Hallaz/KLORID/hardware/case/Alternate Case Design/Tenting Legs/images/choc-sofle-2.jpg

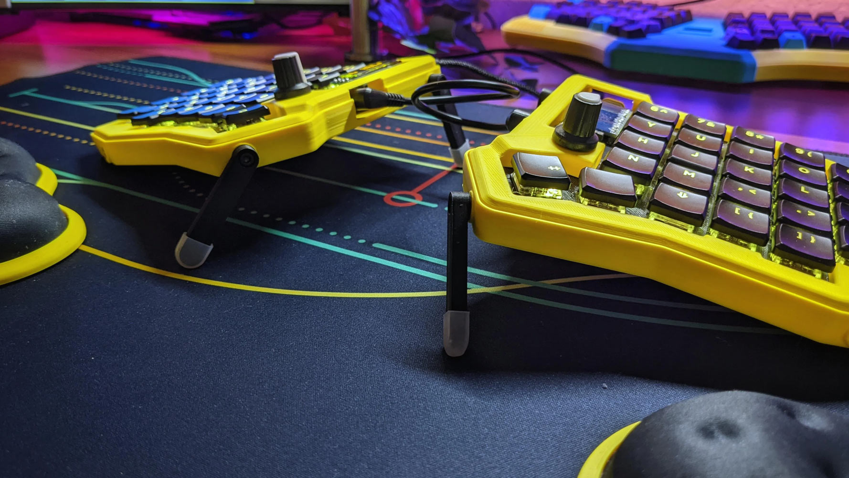
hardware/case/Alternate Case Design/Tenting Legs/images/choc-sofle-2.jpg
