Hallaz/KLORID/hardware/case/Alternate Case Design/Tenting Legs/images/tentingLeg26mm.png

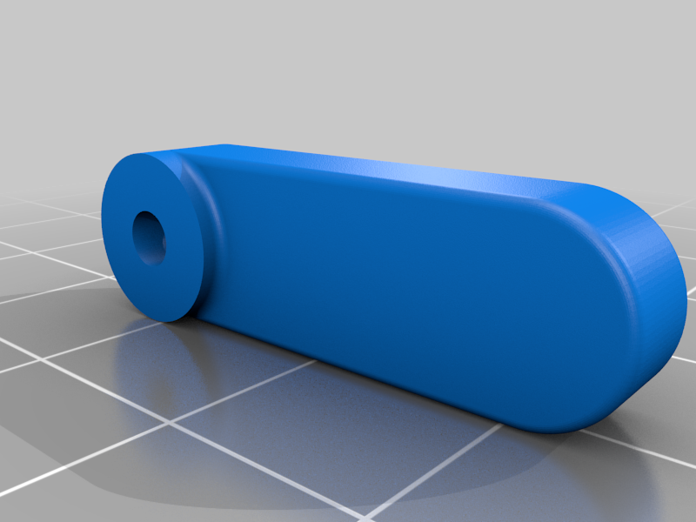
hardware/case/Alternate Case Design/Tenting Legs/images/tentingLeg26mm.png
