Hallaz/KLORID/hardware/case/Alternate Case Design/Tenting Legs/images/TentingLeg38mm.png

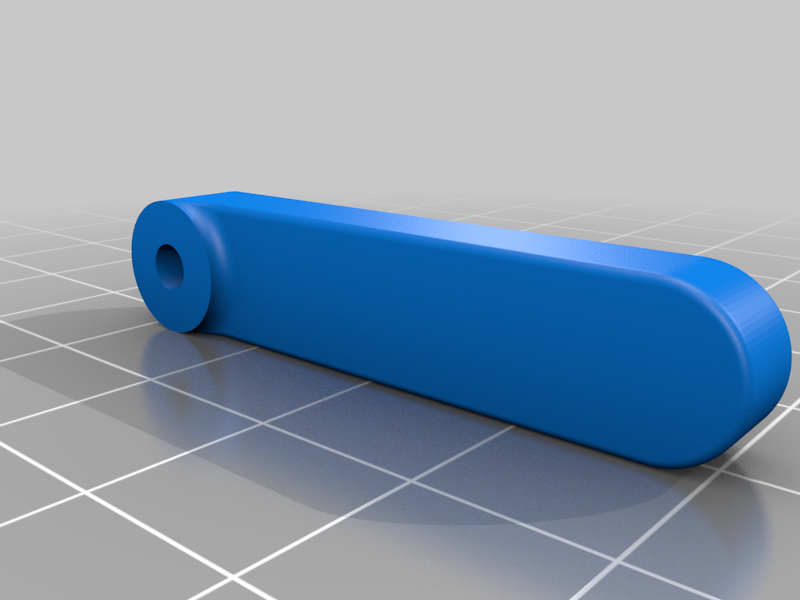
hardware/case/Alternate Case Design/Tenting Legs/images/TentingLeg38mm.png
