Hallaz/KLORID/hardware/case/Alternate Case Design/Tenting Legs/images/tentingLegALT31mm.png

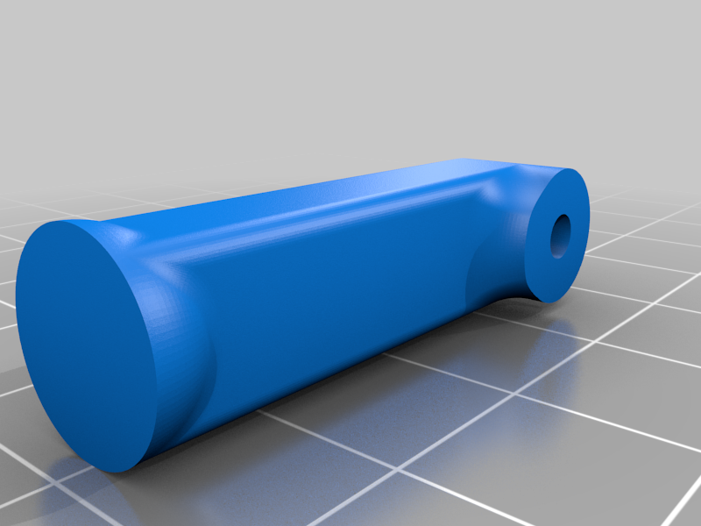
hardware/case/Alternate Case Design/Tenting Legs/images/tentingLegALT31mm.png
