Hallaz/KLORID/hardware/case/Alternate Case Design/Tenting Legs/images/tentingLegALT37mm.png

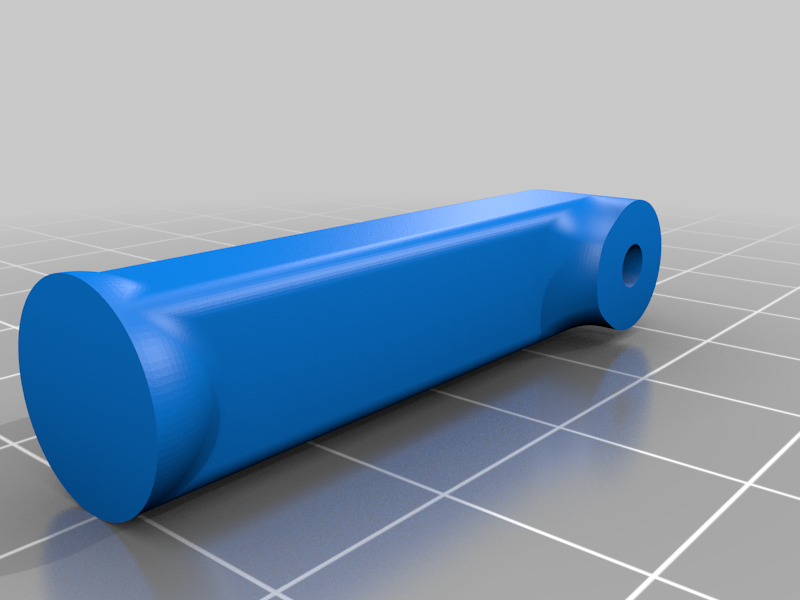
hardware/case/Alternate Case Design/Tenting Legs/images/tentingLegALT37mm.png
