Hallaz/KLORID/hardware/case/docs/images/konrad_3dp.png

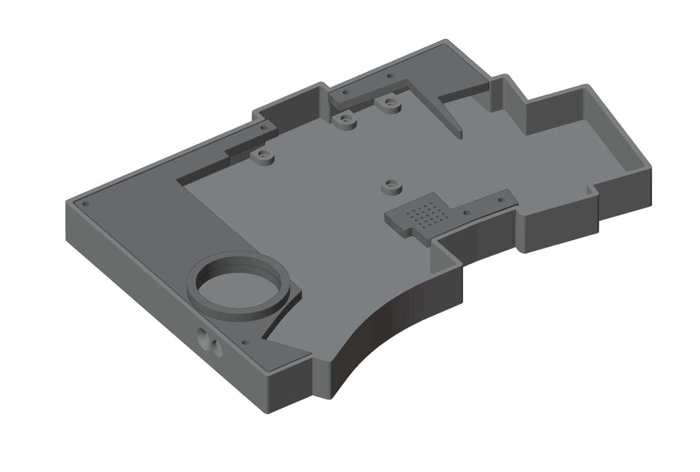
hardware/case/docs/images/konrad_3dp.png
