Hallaz/KLORID/hardware/case/docs/images/konrad_acryl.png

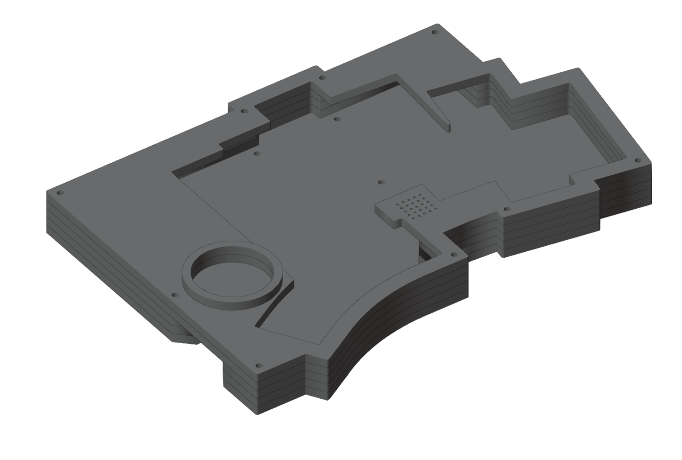
hardware/case/docs/images/konrad_acryl.png
