Hallaz/KLORID/hardware/case/docs/images/saegewerk_3dp_ble_puck.png

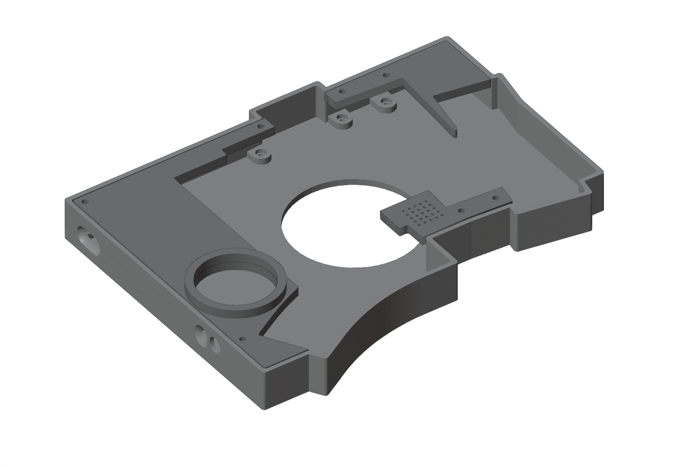
hardware/case/docs/images/saegewerk_3dp_ble_puck.png
