Hallaz/KLORID/hardware/case/docs/images/yubitsume_3dp.png

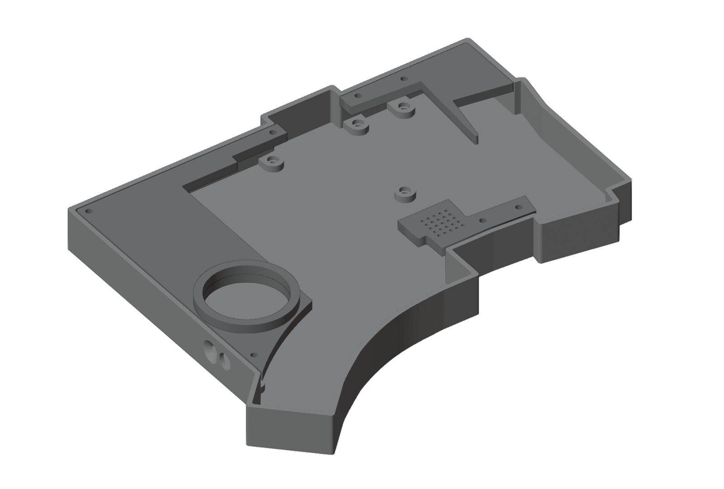
hardware/case/docs/images/yubitsume_3dp.png
