Hallaz/KLORID/hardware/docs/images/Klor_1.4_picture1.png

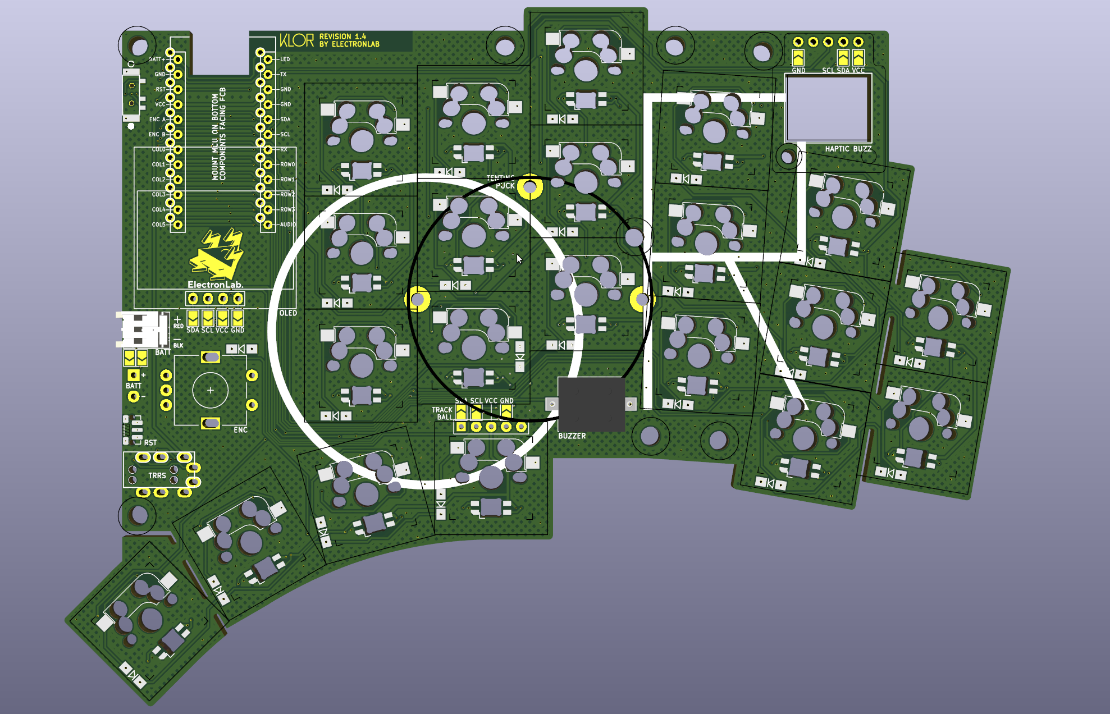
hardware/docs/images/Klor_1.4_picture1.png
