Hallaz/KLORID/hardware/docs/images/Klor_1.4_picture2.png

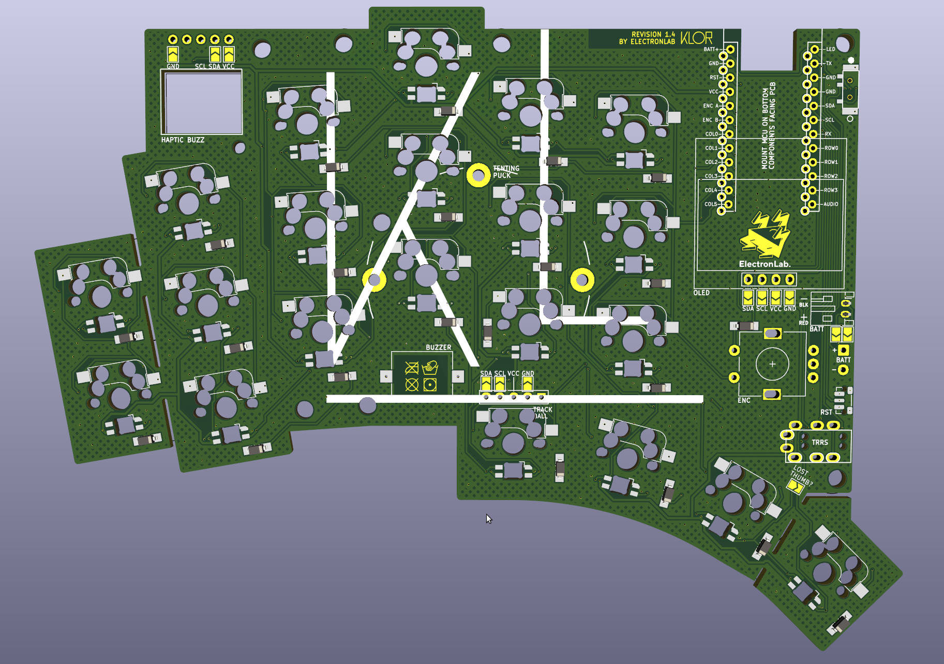
hardware/docs/images/Klor_1.4_picture2.png
