Hallaz/KLORID/hardware/docs/images/Klor_1.4_picture3.png

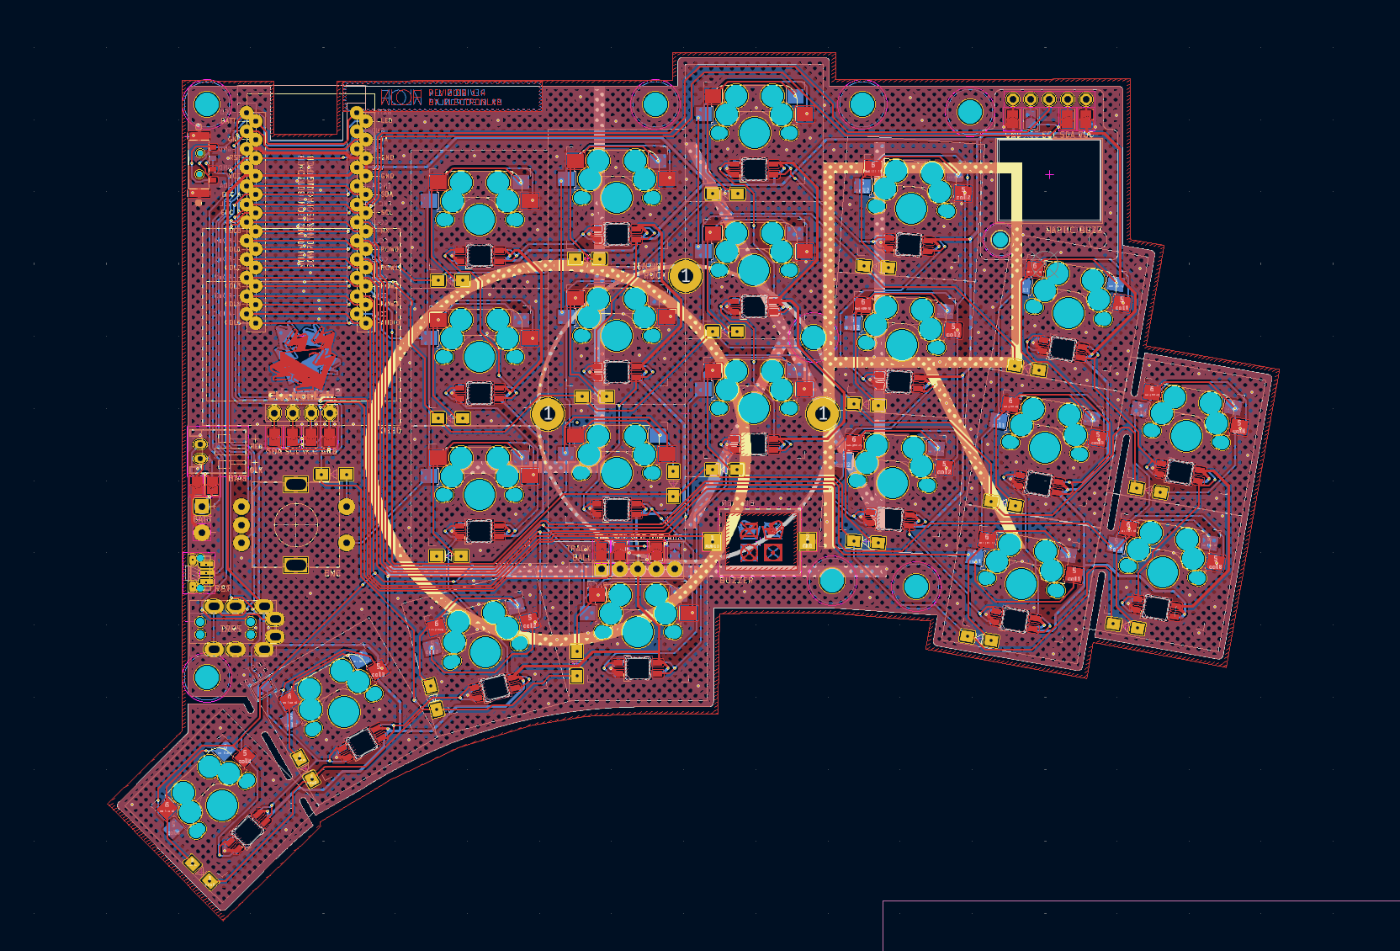
hardware/docs/images/Klor_1.4_picture3.png
