Hallaz/KLORID/hardware/docs/images/Klor_1.4_picture4.png

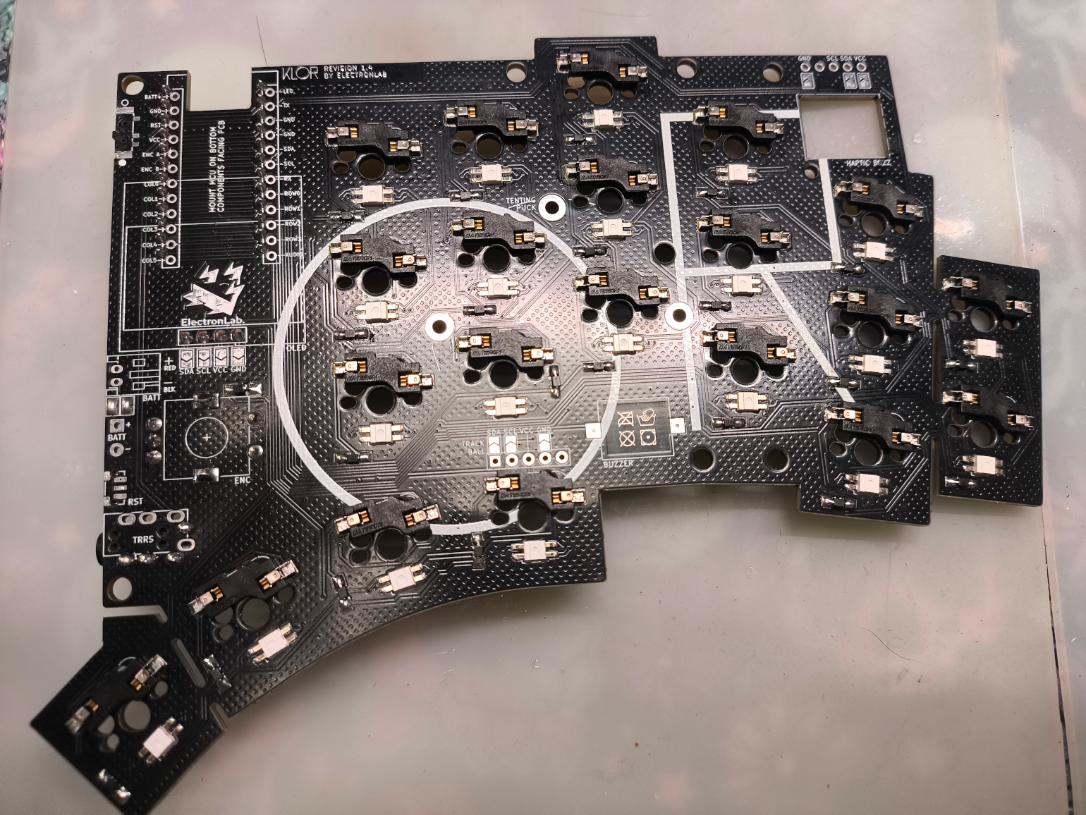
hardware/docs/images/Klor_1.4_picture4.png
