Hallaz/KLORID/hardware/docs/images/Klor_1.4_picture5.png

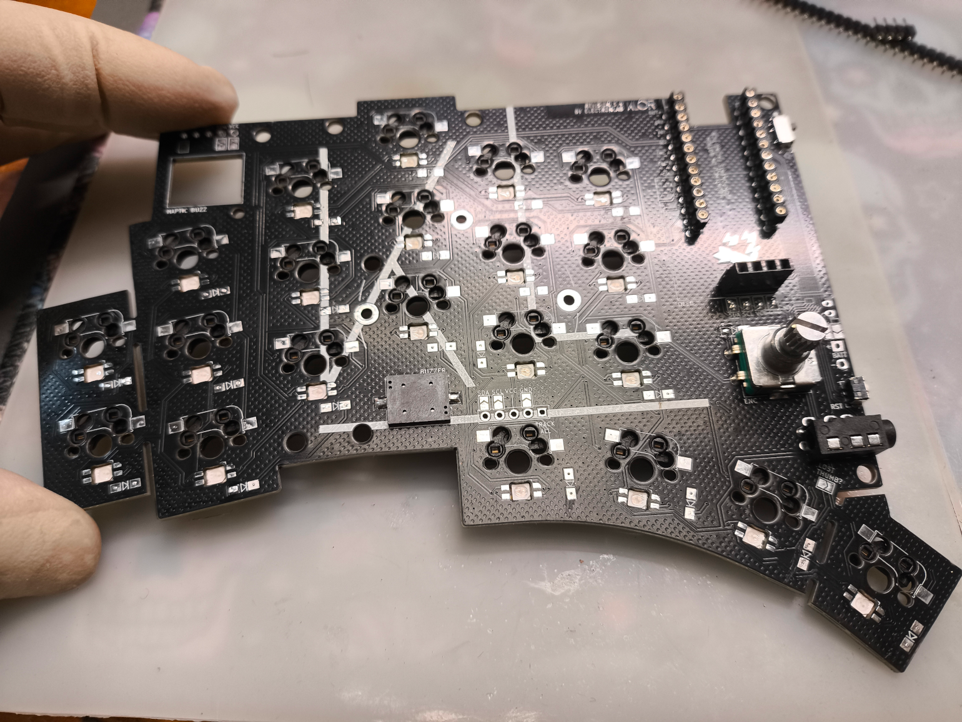
hardware/docs/images/Klor_1.4_picture5.png
