Hallaz/KLORID/hardware/docs/images/Klor_1.4_picture7.png

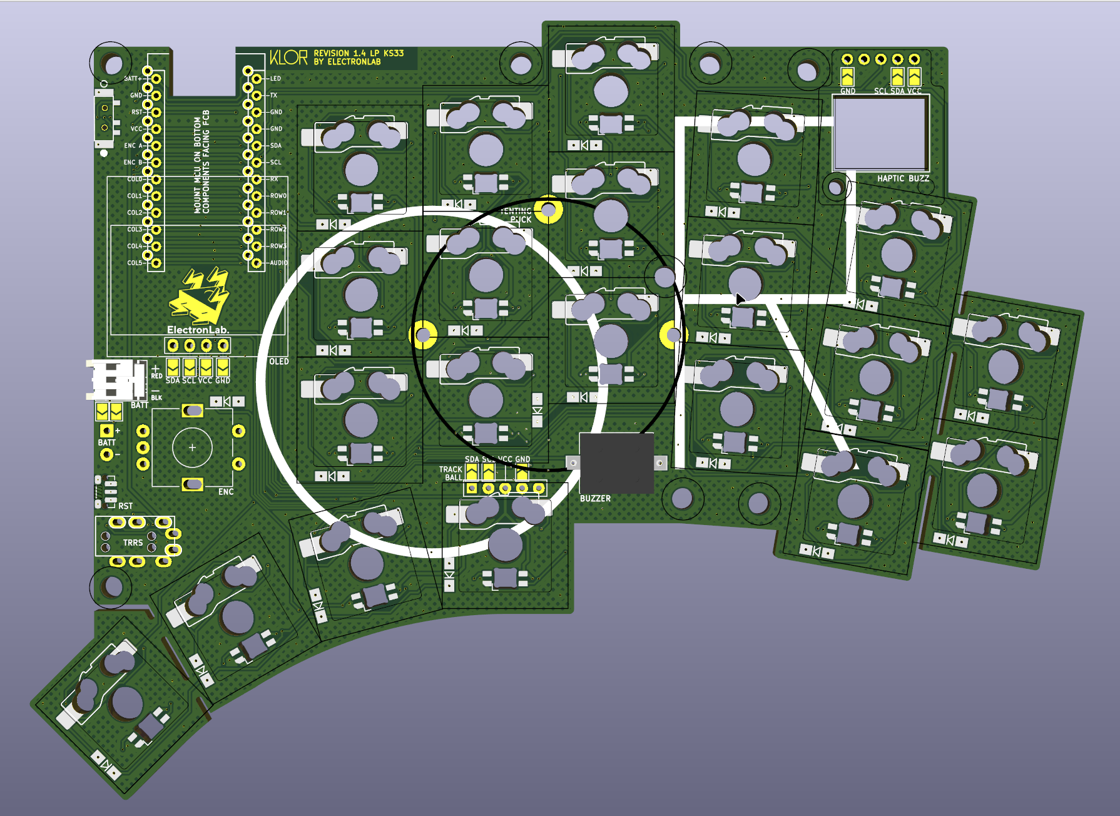
hardware/docs/images/Klor_1.4_picture7.png
