Hallaz/KLORID/hardware/docs/images/Klor_1.4_picture10.png

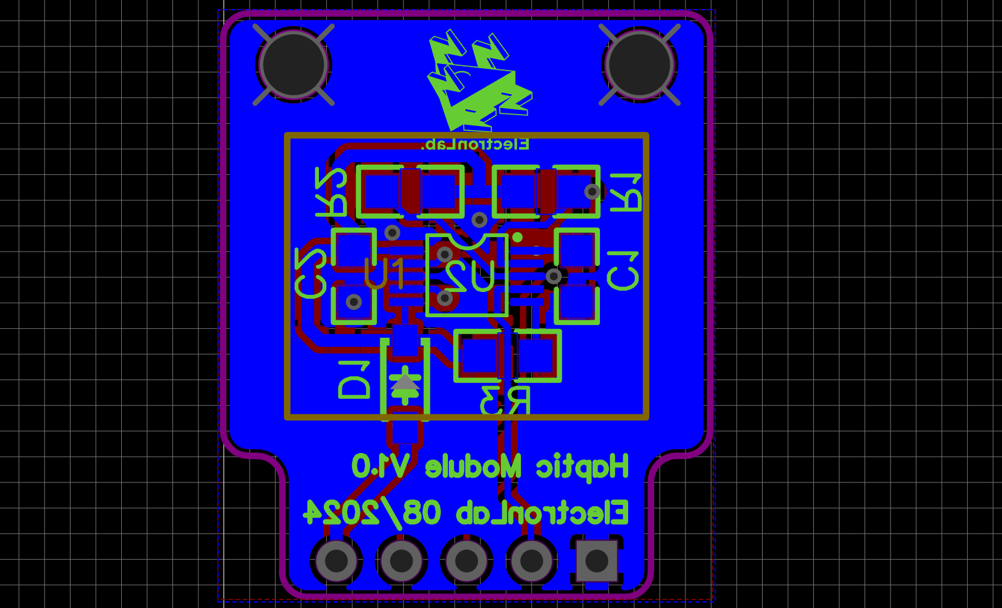
hardware/docs/images/Klor_1.4_picture10.png
