Hallaz/KLORID/hardware/docs/images/Klor_1.4_picture11.png

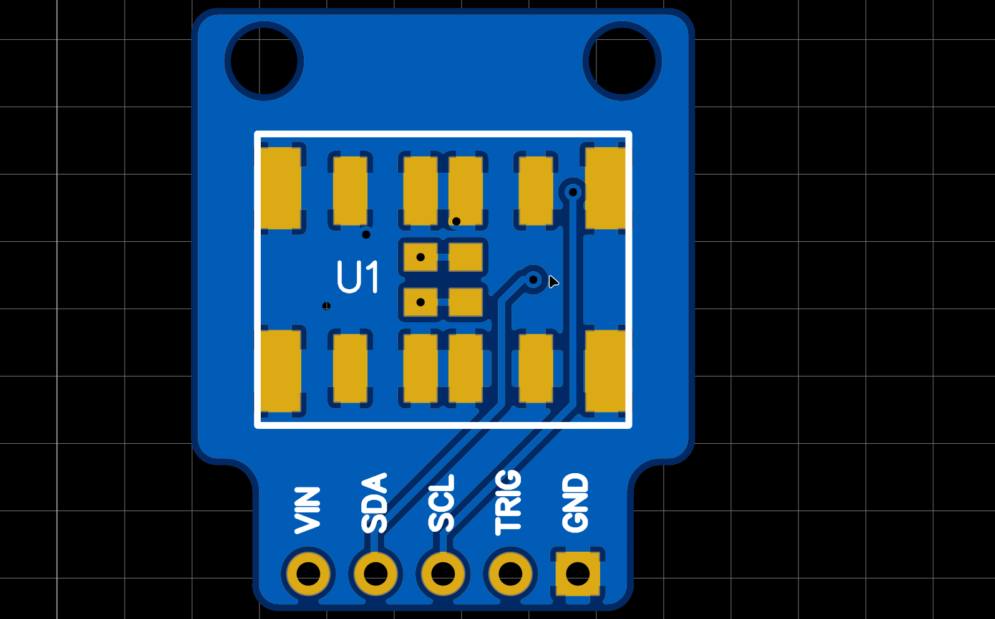
hardware/docs/images/Klor_1.4_picture11.png
