Hallaz/KLORID/hardware/docs/images/Klor_1.4_picture12.png

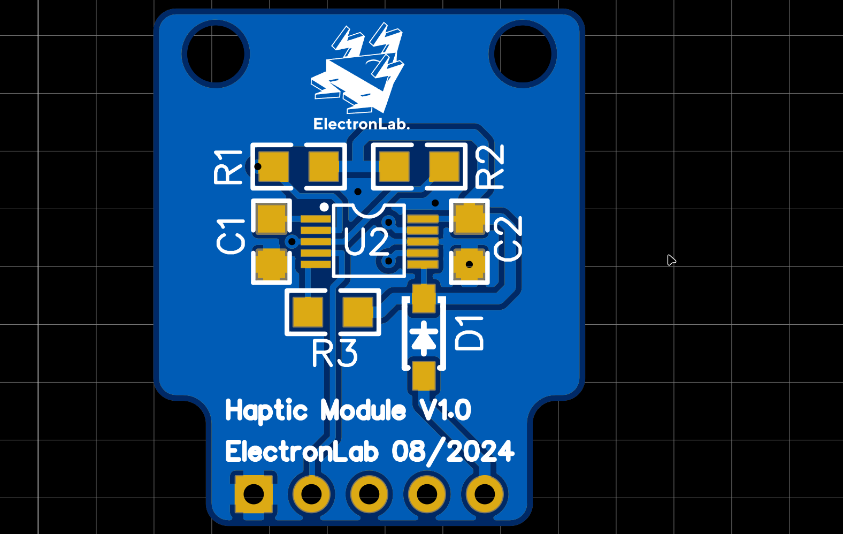
hardware/docs/images/Klor_1.4_picture12.png
