Hallaz/KLORID/hardware/docs/images/Klor_1.4_picture13.png

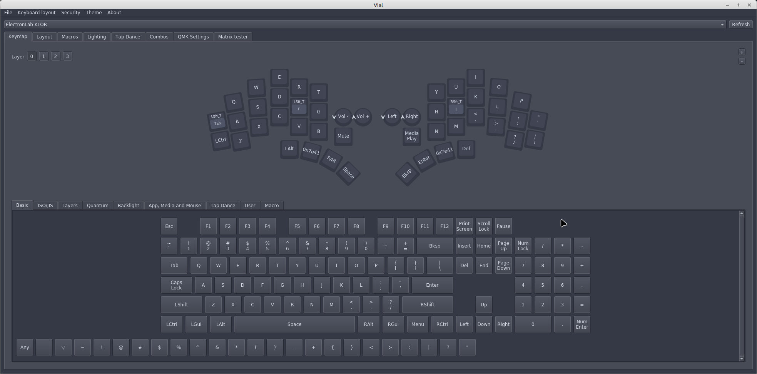
hardware/docs/images/Klor_1.4_picture13.png
