Hallaz/KLORID/hardware/docs/images/KLOR_1.5_picture1.png

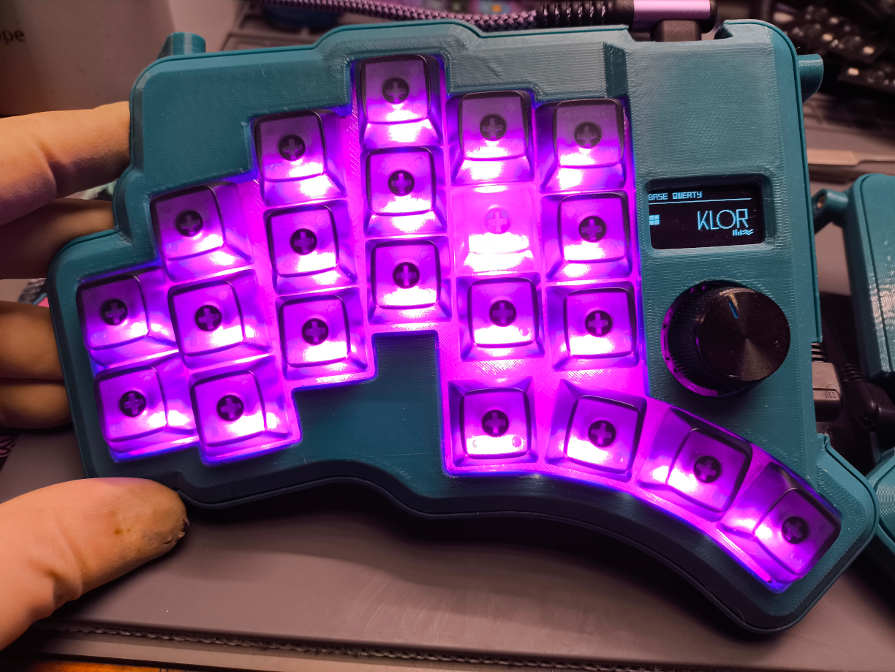
hardware/docs/images/KLOR_1.5_picture1.png
