Hallaz/KLORID/hardware/docs/images/KLOR_1.5_picture2.png

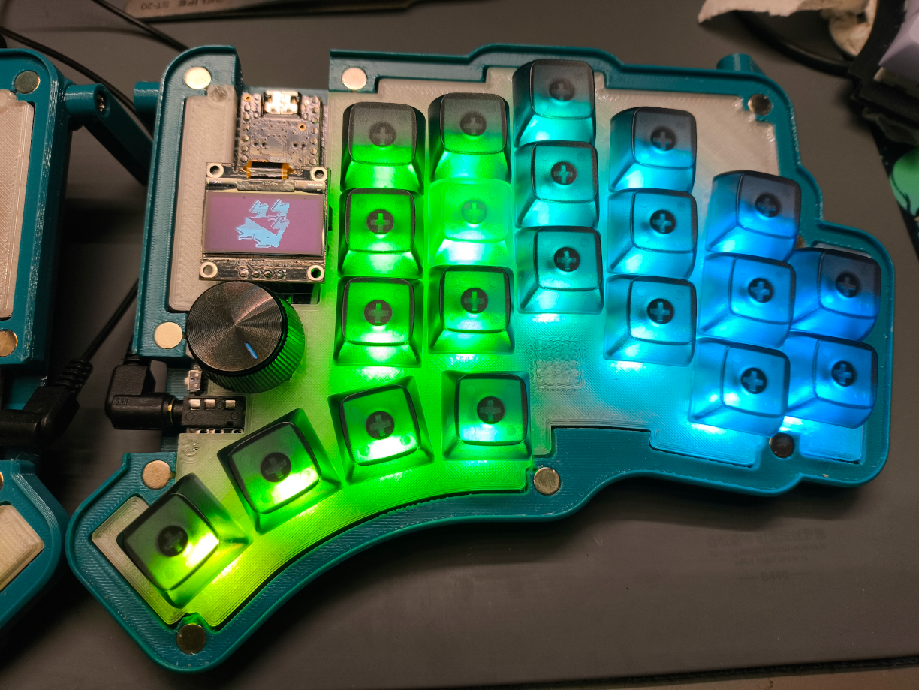
hardware/docs/images/KLOR_1.5_picture2.png
