Hallaz/KLORID/hardware/docs/images/KLOR_1.5_picture4.png

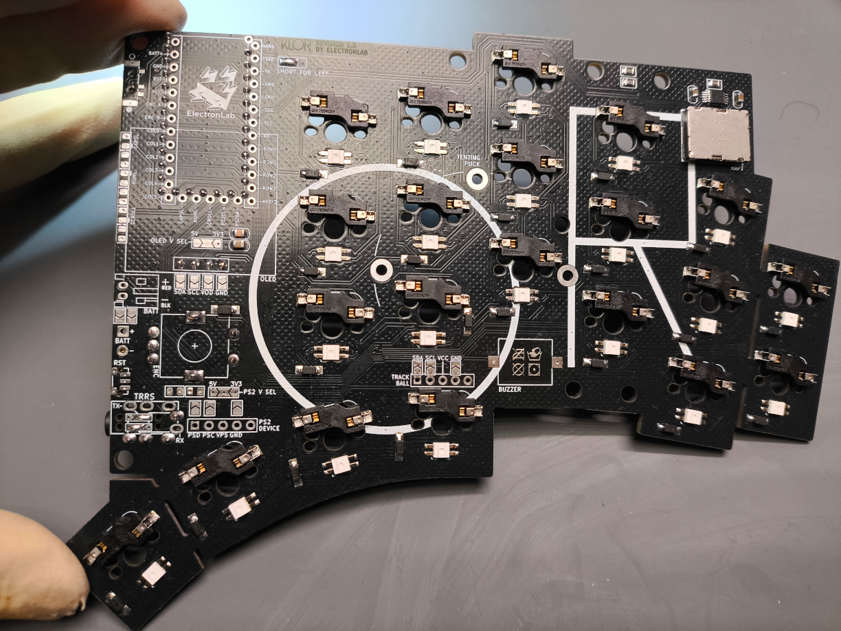
hardware/docs/images/KLOR_1.5_picture4.png
