Hallaz/KLORID/hardware/docs/images/KLOR_1.5_picture5.png

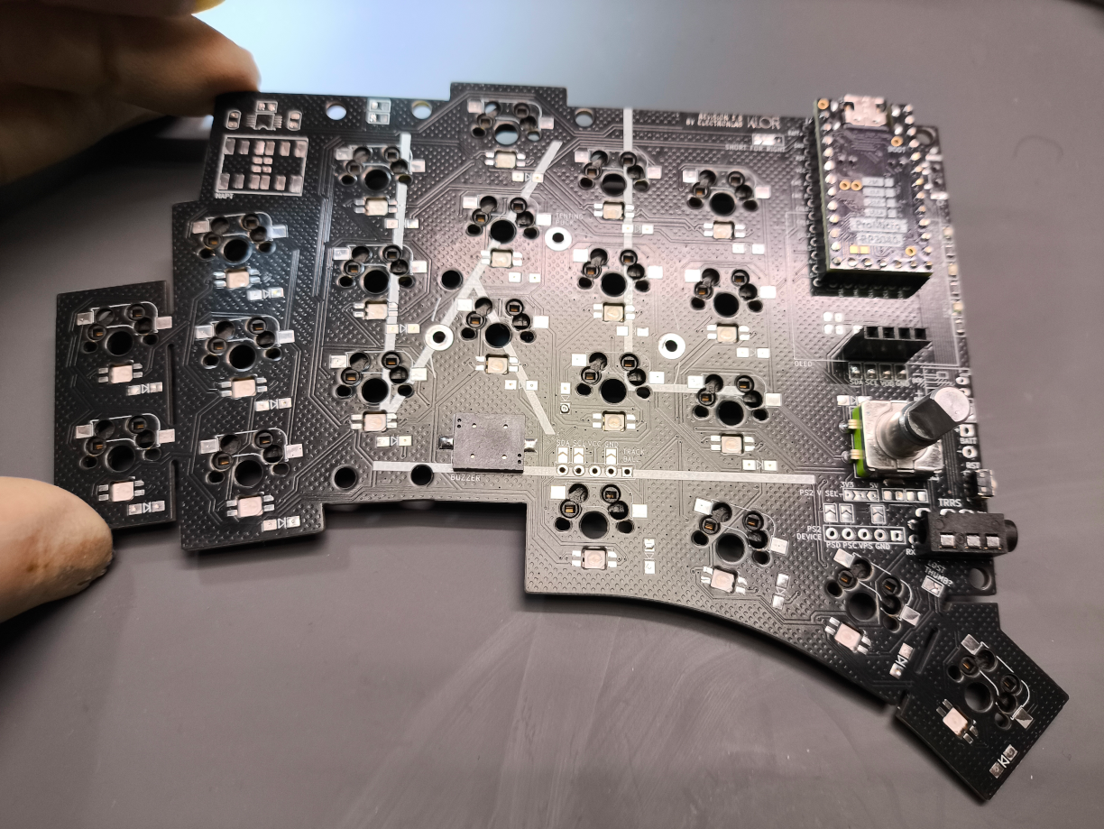
hardware/docs/images/KLOR_1.5_picture5.png
