Hallaz/KLORID/hardware/docs/images/KLOR_knob1-2.png

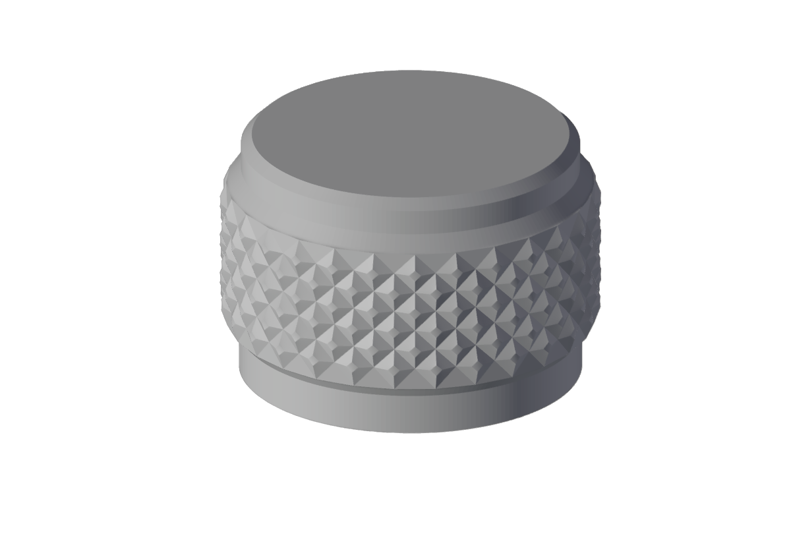
hardware/docs/images/KLOR_knob1-2.png
