Hallaz/KLORID/hardware/docs/images/KLOR_knob_resin_nylon.jpg

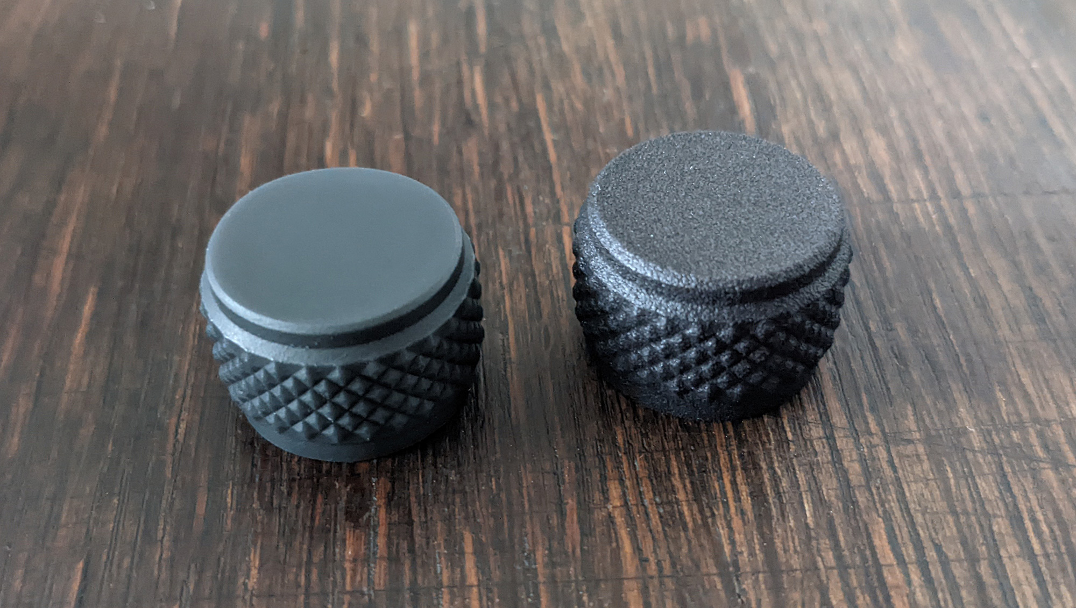
hardware/docs/images/KLOR_knob_resin_nylon.jpg
