Hallaz/KLORID/hardware/docs/images/KLOR_polydactyl_DES01.jpg

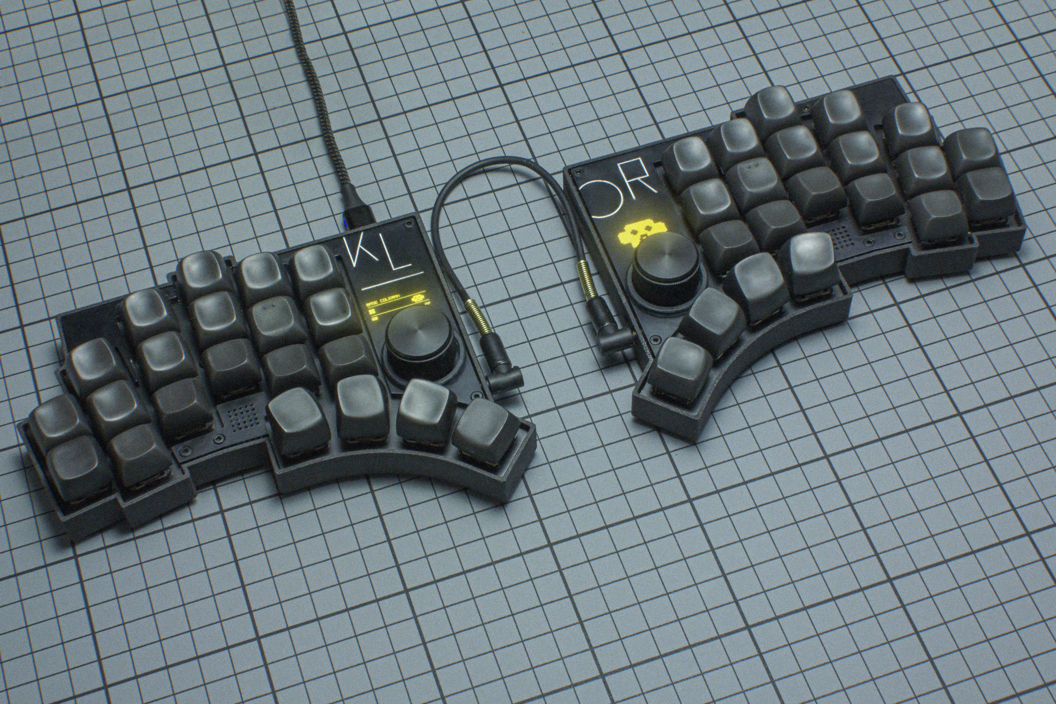
hardware/docs/images/KLOR_polydactyl_DES01.jpg
