Hallaz/KLORID/hardware/docs/images/KLOR_polydactyl_DES02.jpg

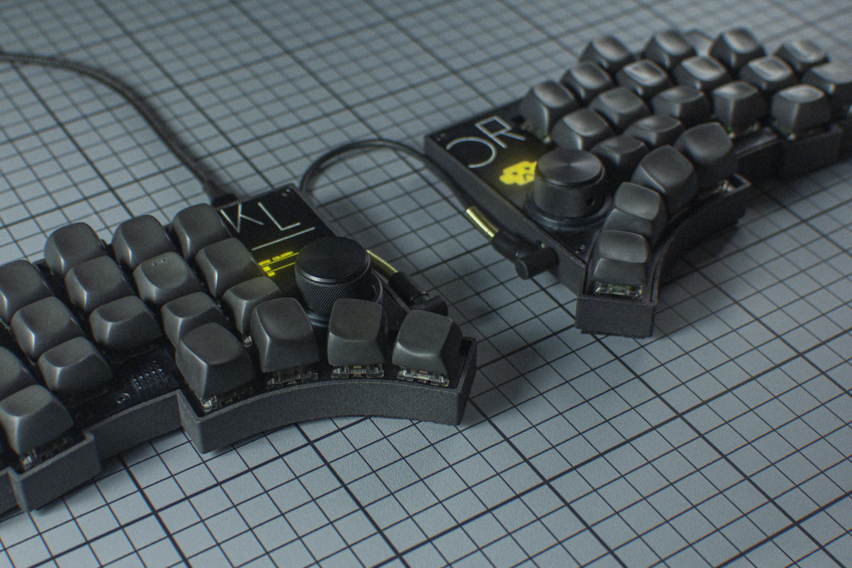
hardware/docs/images/KLOR_polydactyl_DES02.jpg
