Hallaz/KLORID/hardware/docs/images/KLOR_saegewerk_GRID01.jpg

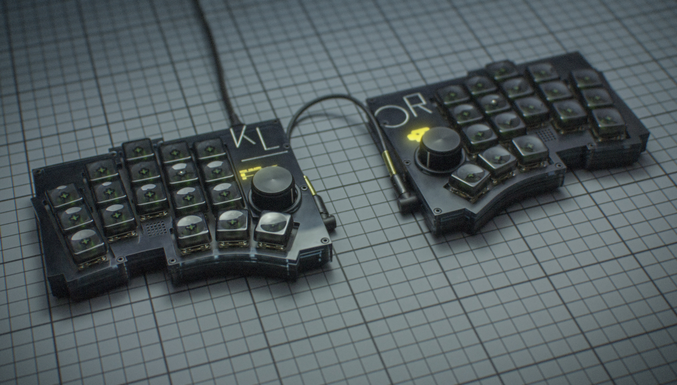
hardware/docs/images/KLOR_saegewerk_GRID01.jpg
