Hallaz/KLORID/hardware/docs/images/KLOR_saegewerk_GRID02.jpg

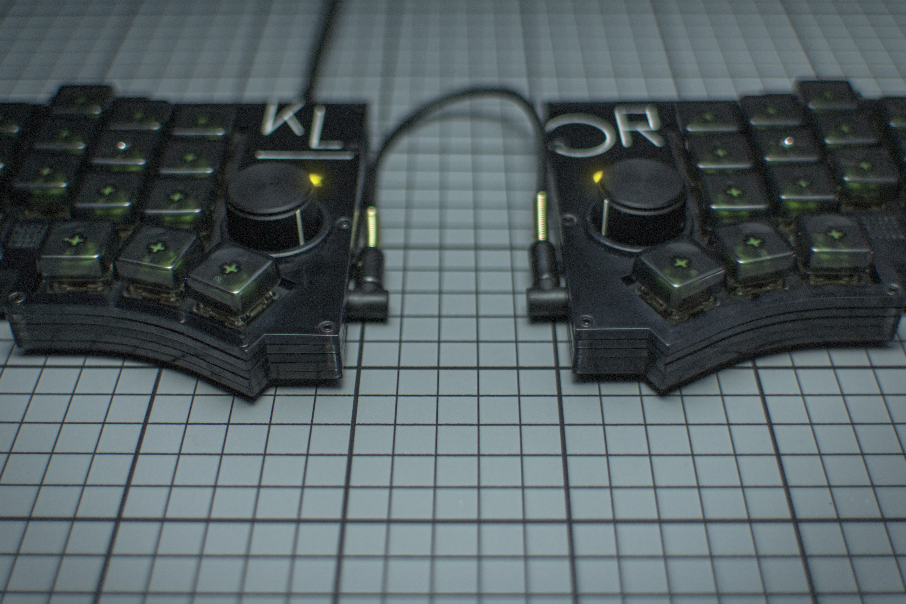
hardware/docs/images/KLOR_saegewerk_GRID02.jpg
