Hallaz/KLORID/hardware/docs/images/KLORpcb.png

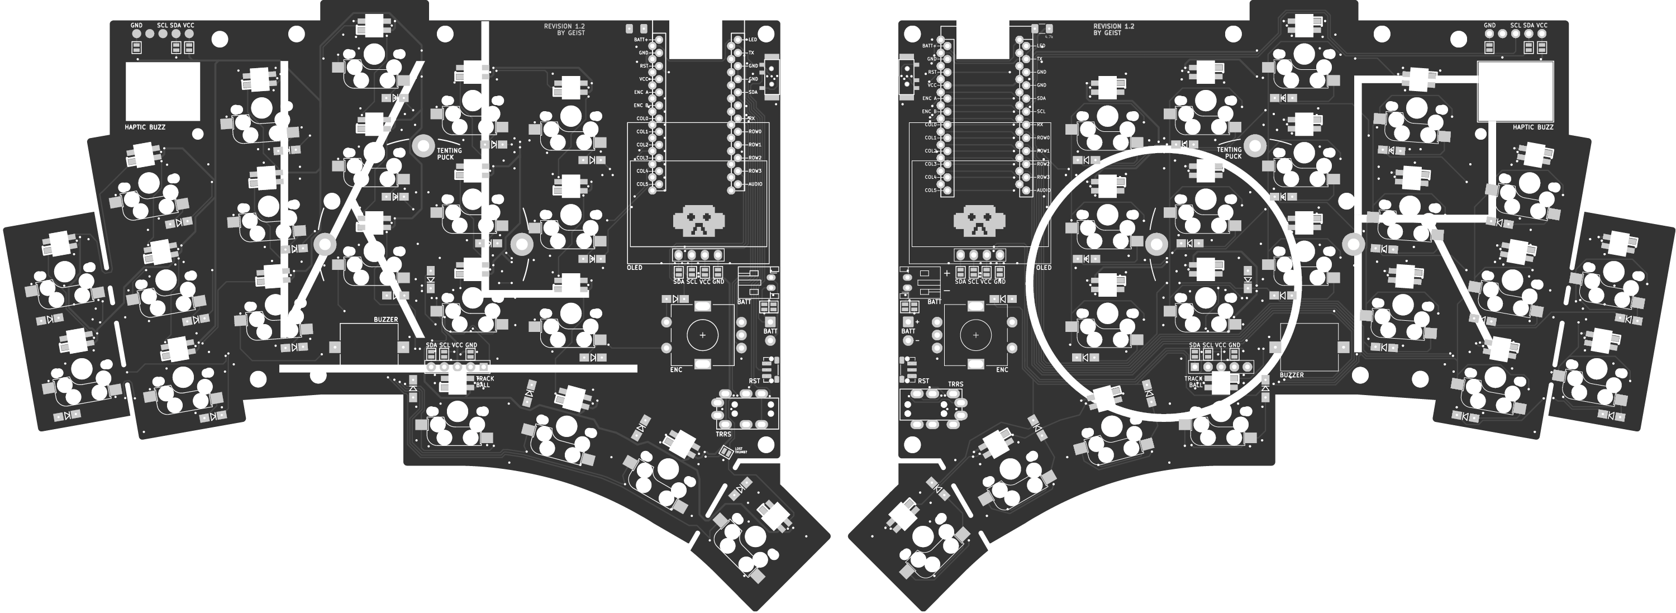
hardware/docs/images/KLORpcb.png
