Hallaz/KLORID/hardware/docs/images/KLORpinout.png

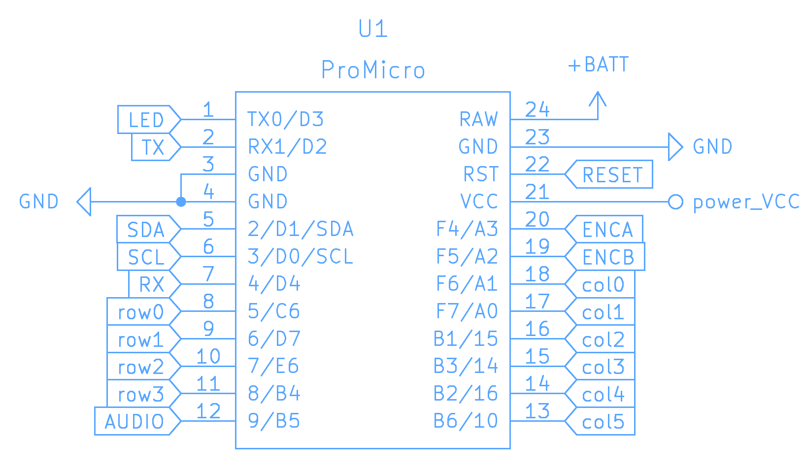
hardware/docs/images/KLORpinout.png
