Hallaz/KLORID/hardware/docs/images/KLORtraces.png

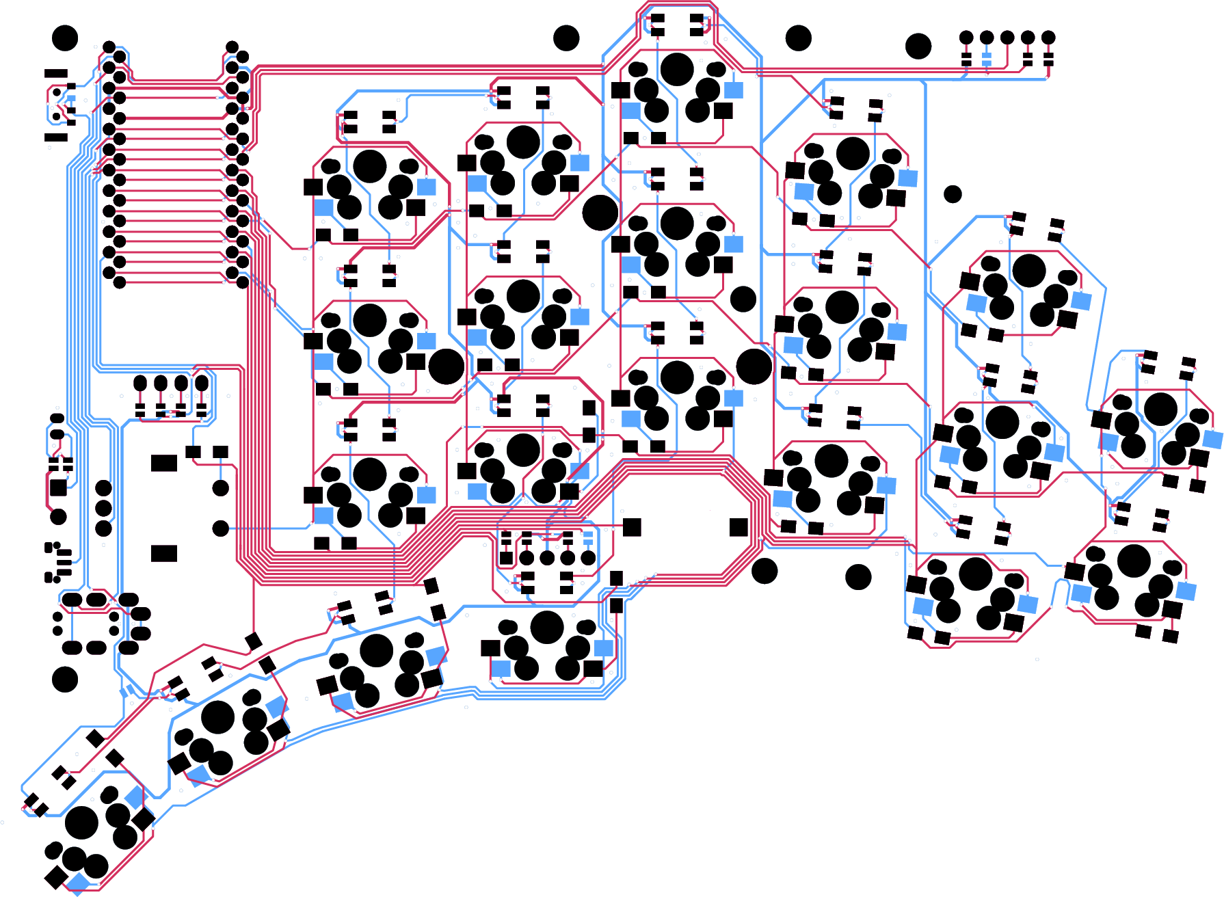
hardware/docs/images/KLORtraces.png
