Hallaz/KLORID/hardware/case/Alternate Case Design/Konrad/BaseWithTenting-Konrad.stl

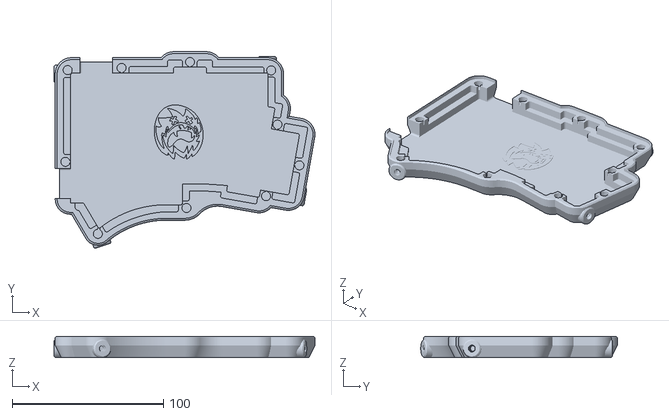
[picture p56: CAD file, 2026-05-15]
hardware/case/Alternate Case Design/Konrad/BaseWithTenting-Konrad.stl
172.8 x 130.1 x 14.0
