Hallaz/KLORID/hardware/case/Alternate Case Design/Polydactyl/v2-GasketBase.stl

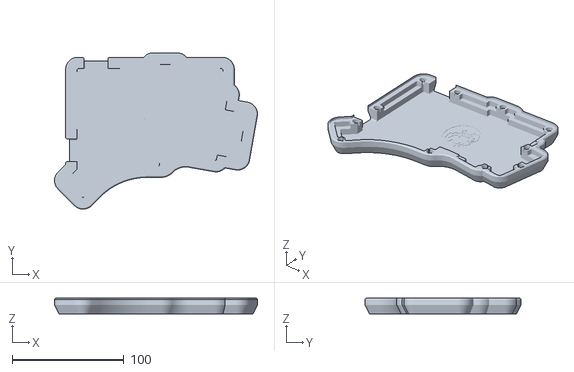
[picture p57: CAD file, 2026-05-15]
hardware/case/Alternate Case Design/Polydactyl/v2-GasketBase.stl
182.0 x 140.1 x 14.0
