Hallaz/KLORID/hardware/case/Alternate Case Design/Saegewerk/v1-Base-Saegewerk.stl

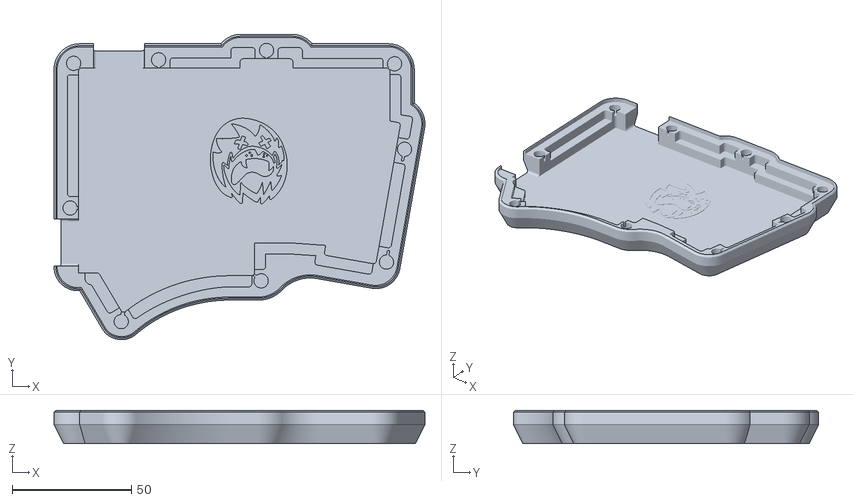
[picture p58: CAD file, 2026-05-15]
hardware/case/Alternate Case Design/Saegewerk/v1-Base-Saegewerk.stl
155.7 x 128.2 x 14.0
