Hallaz/KLORID/hardware/case/Alternate Case Design/Tenting Legs/files/tentingLeg42mm.stl

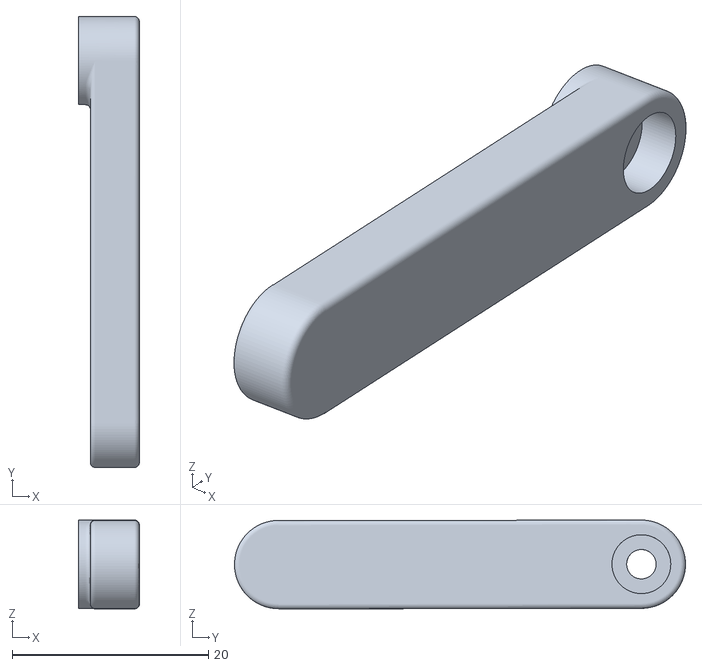
[picture p59: CAD file, 2026-05-15]
hardware/case/Alternate Case Design/Tenting Legs/files/tentingLeg42mm.stl
6.21 x 46.0 x 9.07
