Hallaz/KLORID/hardware/case/Alternate Case Design/Yubitsume/v1-Base-Yubitmsume.stl

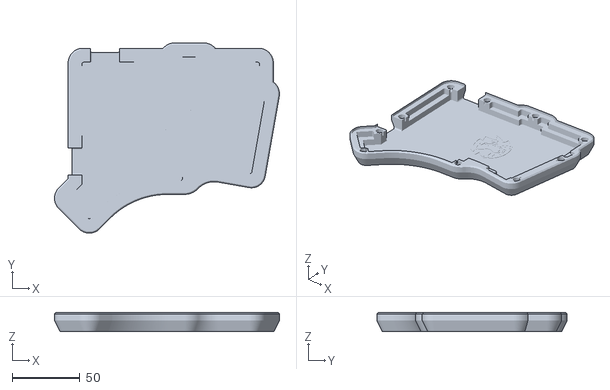
[picture p60: CAD file, 2026-05-15]
hardware/case/Alternate Case Design/Yubitsume/v1-Base-Yubitmsume.stl
165.8 x 140.1 x 14.0
