Hallaz/KLORID/hardware/case/3DP/konrad/acrylic/KLOR_konrad_3DPcase_acrylic_logotype.dxf

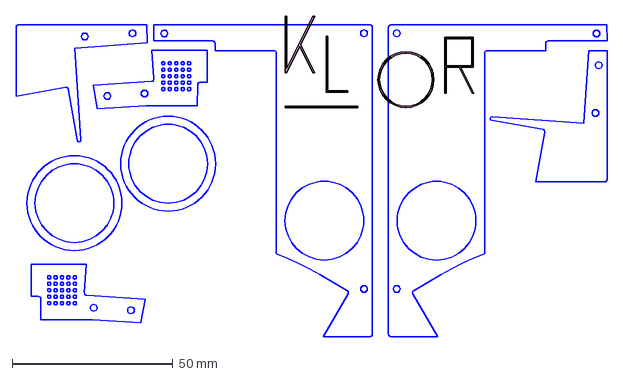
[picture p61: CAD file, 2026-05-15]
hardware/case/3DP/konrad/acrylic/KLOR_konrad_3DPcase_acrylic_logotype.dxf
183.6 x 99.5 mm
