Hallaz/KLORID/hardware/case/3DP/konrad/regular/KLOR_konrad_case_L.stl

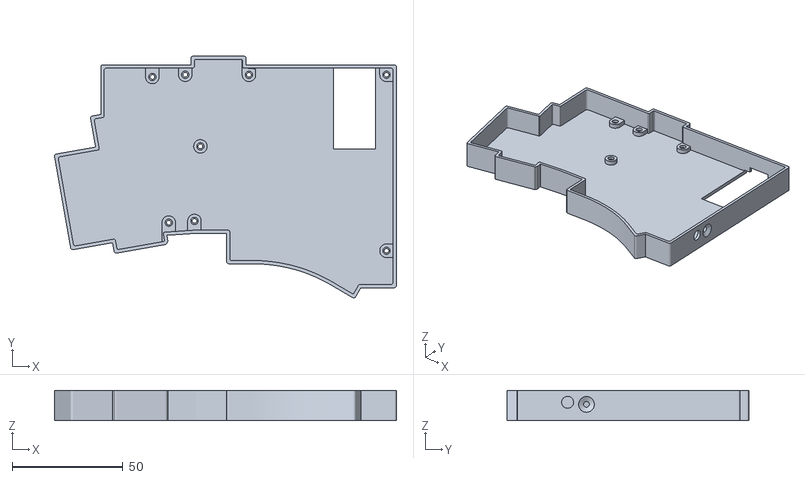
[picture p62: CAD file, 2026-05-15]
hardware/case/3DP/konrad/regular/KLOR_konrad_case_L.stl
154.3 x 109.2 x 13.6
