Hallaz/KLORID/hardware/case/3DP/polydactyl/acrylic/KLOR_polydactyl_3DPcase_acrylic_logotype.dxf

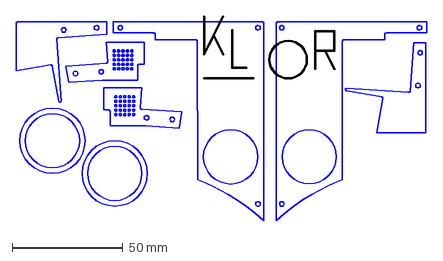
[picture p63: CAD file, 2026-05-15]
hardware/case/3DP/polydactyl/acrylic/KLOR_polydactyl_3DPcase_acrylic_logotype.dxf
185.0 x 92.4 mm
