Hallaz/KLORID/hardware/case/3DP/saegewerk/acrylic/KLOR_saegewerk_3DPcase_acrylic_logotype.dxf

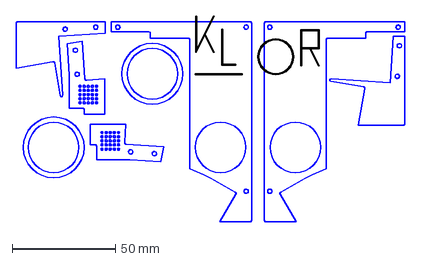
[picture p64: CAD file, 2026-05-15]
hardware/case/3DP/saegewerk/acrylic/KLOR_saegewerk_3DPcase_acrylic_logotype.dxf
188.1 x 99.5 mm
