Hallaz/KLORID/hardware/case/3DP/saegewerk/bluetooth/KLOR_saegewerk_case_ble_L.stl

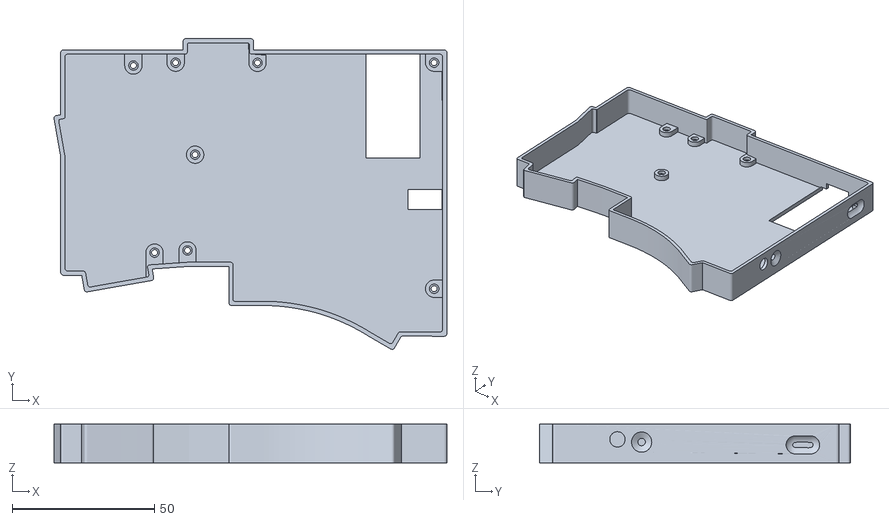
[picture p65: CAD file, 2026-05-15]
hardware/case/3DP/saegewerk/bluetooth/KLOR_saegewerk_case_ble_L.stl
138.1 x 109.2 x 13.6
