Hallaz/KLORID/hardware/case/3DP/yubitsume/acrylic/KLOR_yubitsume_3DPcase_acrylic_logotype.dxf

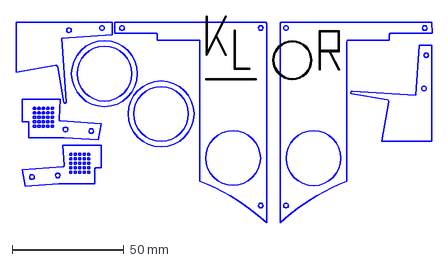
[picture p66: CAD file, 2026-05-15]
hardware/case/3DP/yubitsume/acrylic/KLOR_yubitsume_3DPcase_acrylic_logotype.dxf
186.0 x 92.4 mm
