Hallaz/KLORID/hardware/case/3DP/yubitsume/bluetooth/KLOR_yubitsume_case_puck_ble_R.stl

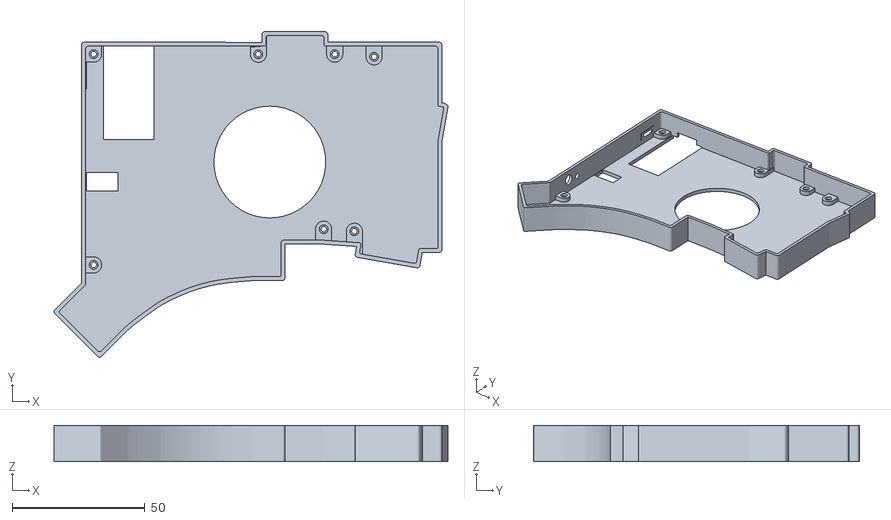
[picture p67: CAD file, 2026-05-15]
hardware/case/3DP/yubitsume/bluetooth/KLOR_yubitsume_case_puck_ble_R.stl
148.4 x 122.7 x 13.6
