Hallaz/KLORID/hardware/case/Alternate Case Design/EncoderInsert-flat.stl

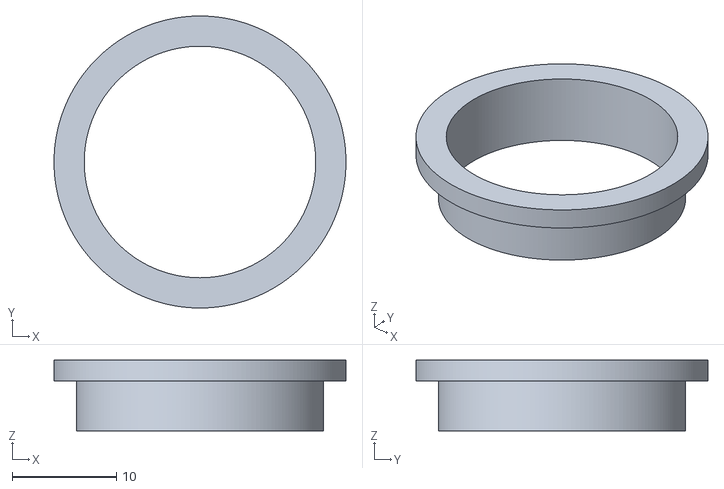
[picture p68: CAD file, 2026-05-15]
hardware/case/Alternate Case Design/EncoderInsert-flat.stl
28.0 x 28.0 x 6.80
