Hallaz/KLORID/hardware/case/Alternate Case Design/Konrad/SwitchPlate-Konrad.stl

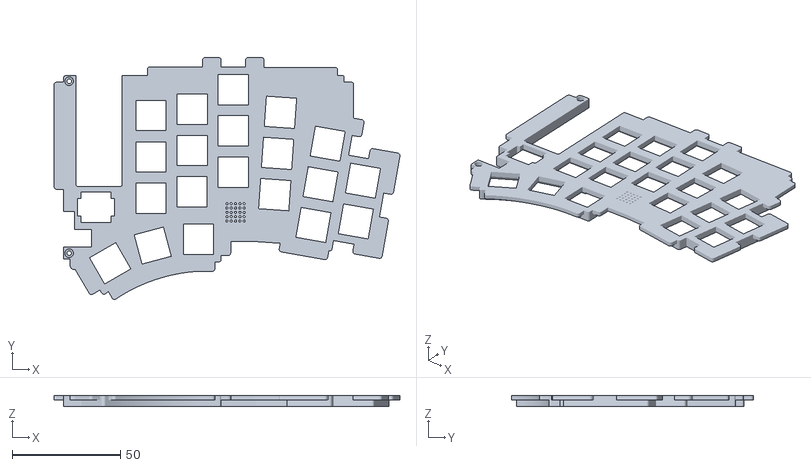
[picture p69: CAD file, 2026-05-15]
hardware/case/Alternate Case Design/Konrad/SwitchPlate-Konrad.stl
159.8 x 111.8 x 5.00
