Hallaz/KLORID/hardware/case/Alternate Case Design/Polydactyl/v2-GasketSwitchPlate.stl

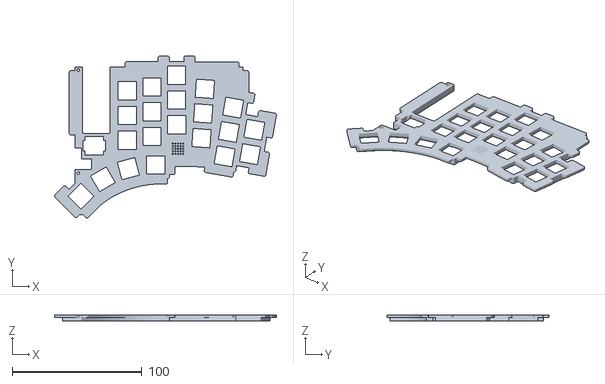
[picture p70: CAD file, 2026-05-15]
hardware/case/Alternate Case Design/Polydactyl/v2-GasketSwitchPlate.stl
171.1 x 124.9 x 5.00
