Hallaz/KLORID/hardware/case/Alternate Case Design/Saegewerk/v1-SwitchPlate-Saegewerk.stl

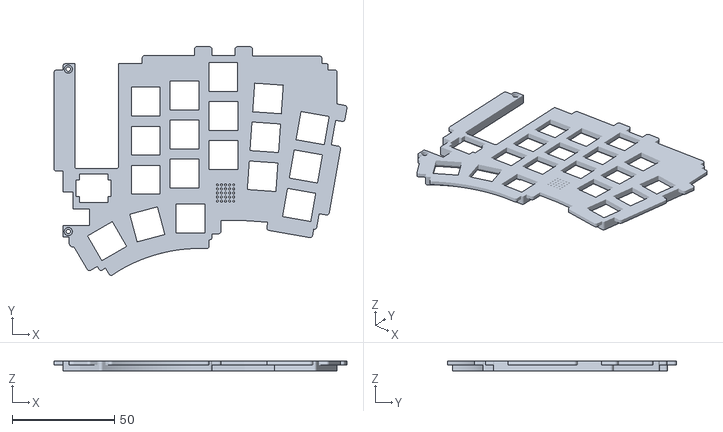
[picture p71: CAD file, 2026-05-15]
hardware/case/Alternate Case Design/Saegewerk/v1-SwitchPlate-Saegewerk.stl
143.2 x 111.8 x 5.00
