Hallaz/KLORID/hardware/case/Alternate Case Design/Tenting Legs/files/tentingleg36mm.stl

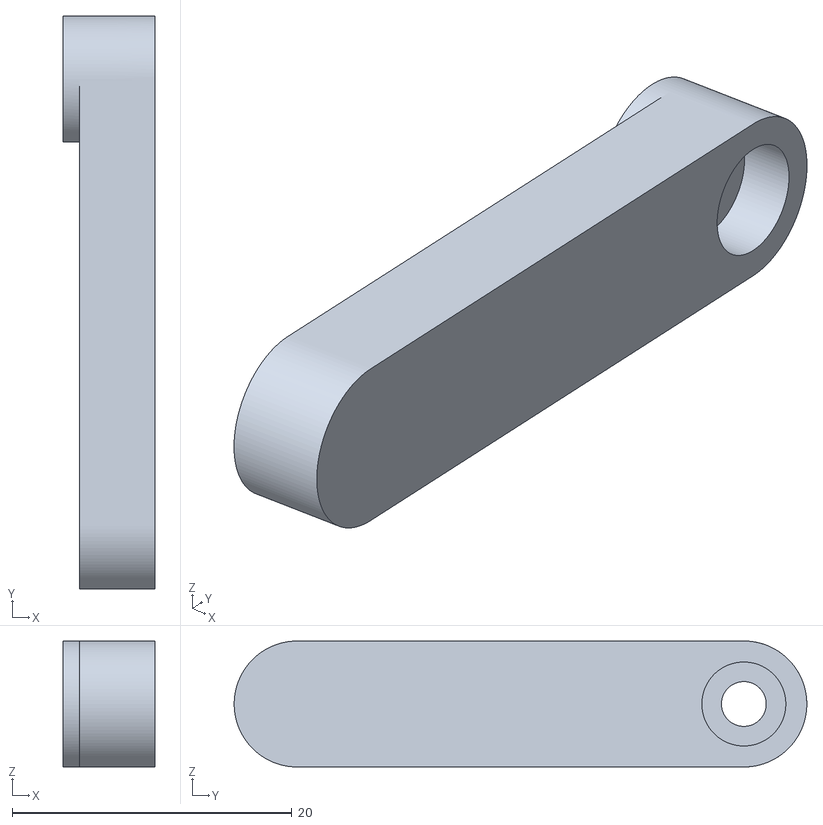
[picture p72: CAD file, 2026-05-15]
hardware/case/Alternate Case Design/Tenting Legs/files/tentingleg36mm.stl
6.60 x 40.9 x 9.00
