Hallaz/KLORID/hardware/case/Alternate Case Design/Yubitsume/v1-Lid-Yubitsume-noOLED.stl

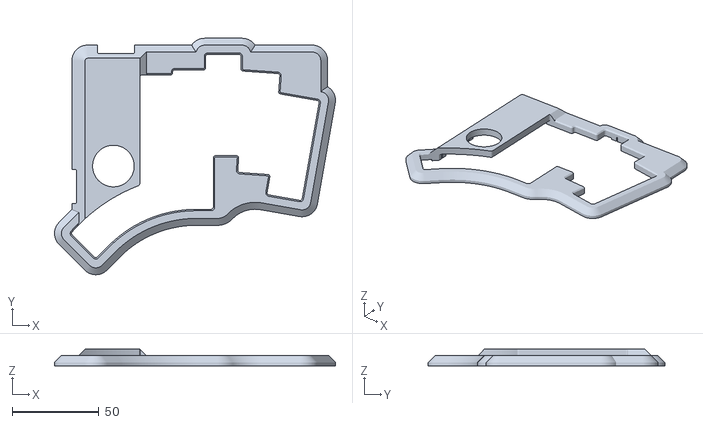
[picture p73: CAD file, 2026-05-15]
hardware/case/Alternate Case Design/Yubitsume/v1-Lid-Yubitsume-noOLED.stl
162.2 x 136.5 x 9.60
