Hallaz/KLORID/hardware/case/3DP/saegewerk/regular/KLOR_saegewerk_case_L.stl

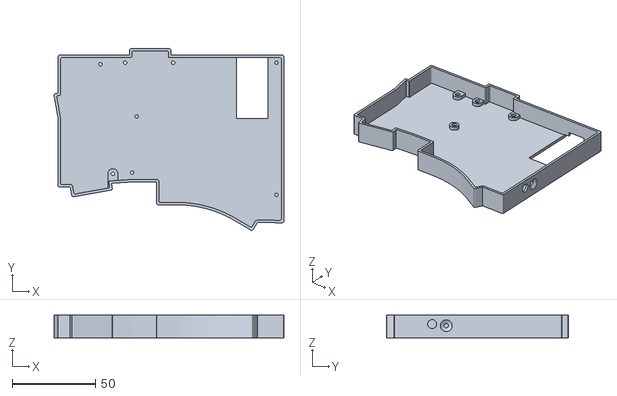
[picture p74: CAD file, 2026-05-15]
hardware/case/3DP/saegewerk/regular/KLOR_saegewerk_case_L.stl
138.1 x 109.2 x 13.6
