Hallaz/KLORID/hardware/case/Alternate Case Design/Polydactyl/v2-GasketBaseWithTenting.stl

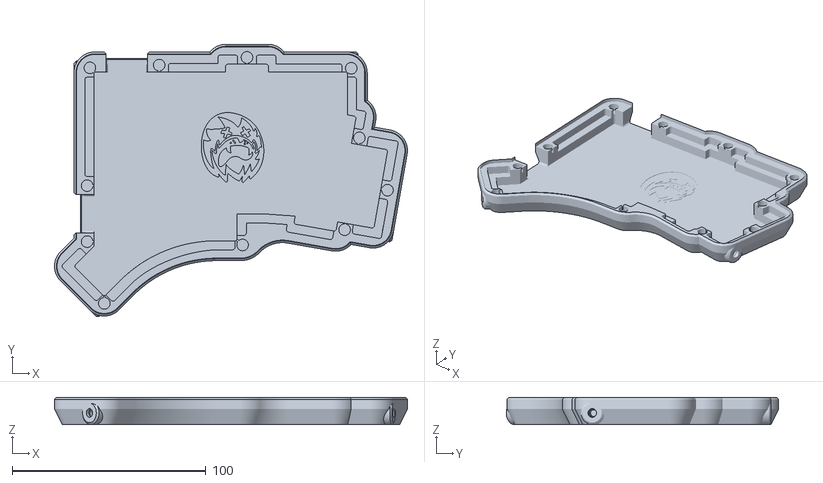
[picture p76: CAD file, 2026-05-15]
hardware/case/Alternate Case Design/Polydactyl/v2-GasketBaseWithTenting.stl
182.0 x 140.5 x 14.0
