Hallaz/KLORID/hardware/case/Alternate Case Design/Tenting Legs/files/TentingLeg38mm.stl

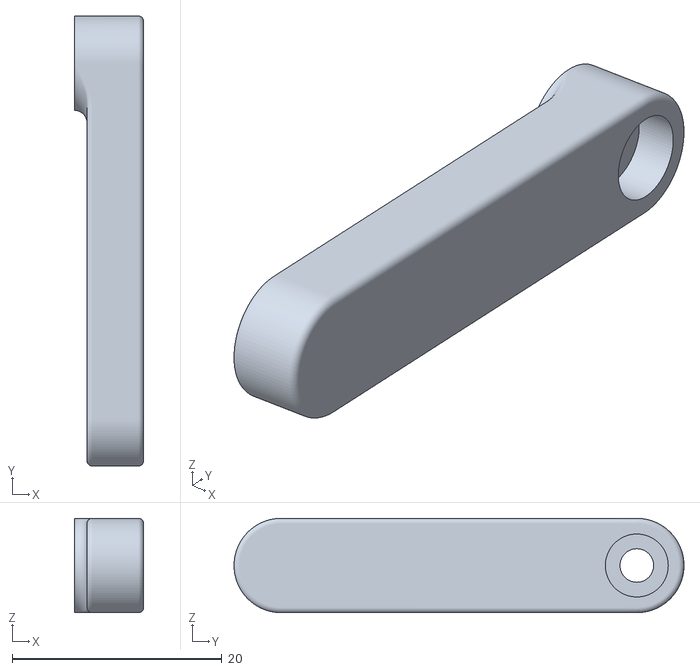
[picture p77: CAD file, 2026-05-15]
hardware/case/Alternate Case Design/Tenting Legs/files/TentingLeg38mm.stl
6.60 x 42.9 x 9.00
