Hallaz/KLORID/hardware/case/Alternate Case Design/Yubitsume/v1-BaseWithTenting-Yubitsume.stl

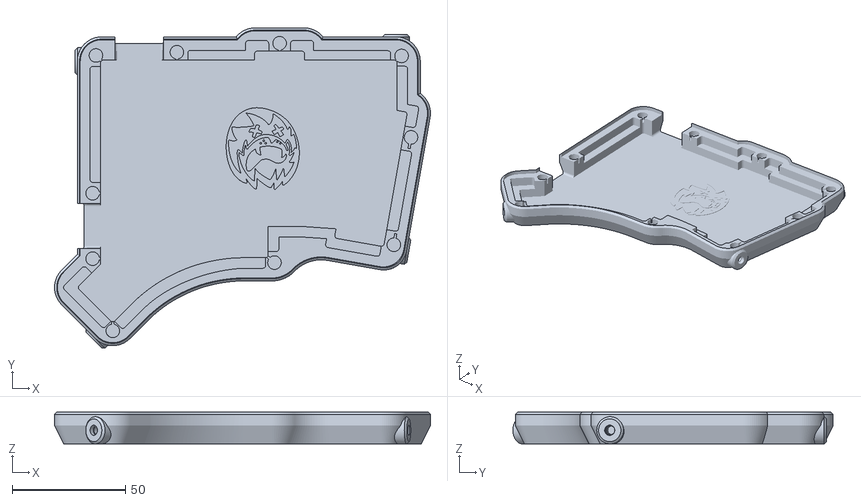
[picture p78: CAD file, 2026-05-15]
hardware/case/Alternate Case Design/Yubitsume/v1-BaseWithTenting-Yubitsume.stl
165.8 x 141.2 x 14.0
