Hallaz/KLORID/hardware/case/Alternate Case Design/EncoderInsert-flat-16mm.stl

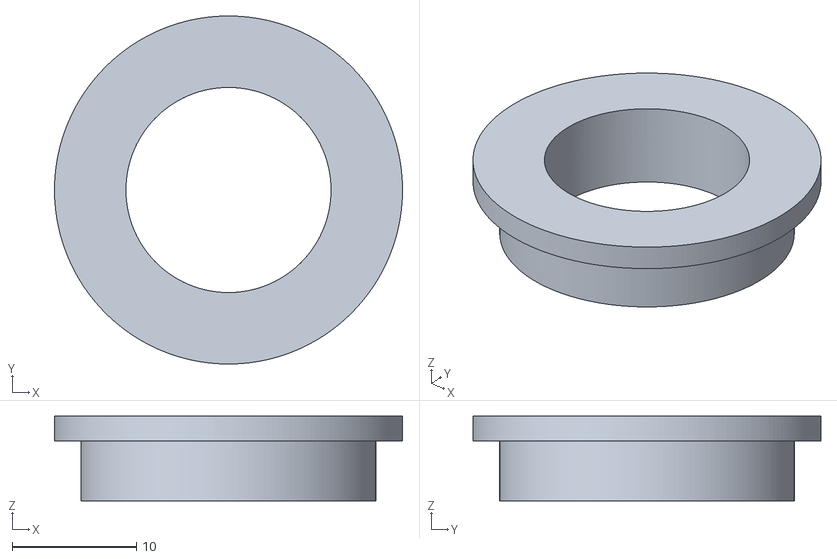
[picture p79: CAD file, 2026-05-15]
hardware/case/Alternate Case Design/EncoderInsert-flat-16mm.stl
28.0 x 28.0 x 6.80
