Hallaz/KLORID/hardware/case/Alternate Case Design/Tenting Legs/files/tentingLeg40mm.stl

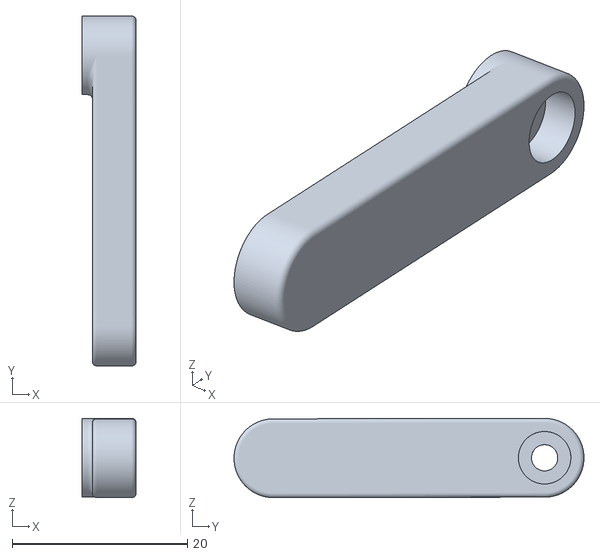
[picture p80: CAD file, 2026-05-15]
hardware/case/Alternate Case Design/Tenting Legs/files/tentingLeg40mm.stl
6.21 x 40.0 x 9.06
