Hallaz/KLORID/hardware/case/Alternate Case Design/Yubitsume/v1-SwitchPlate-Yubitsume.stl

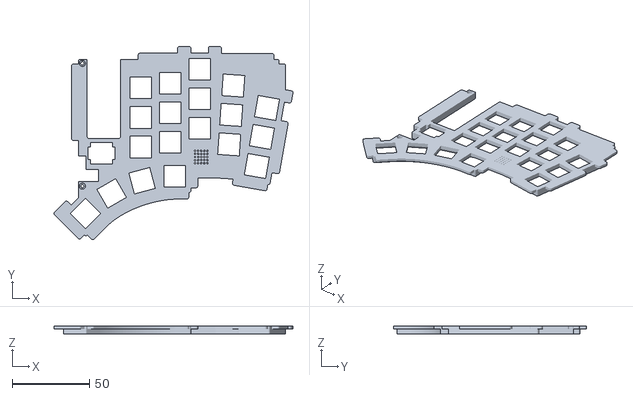
[picture p81: CAD file, 2026-05-15]
hardware/case/Alternate Case Design/Yubitsume/v1-SwitchPlate-Yubitsume.stl
154.6 x 124.9 x 5.00
