Hallaz/KLORID/hardware/case/Alternate Case Design/Tenting Legs/files/tentingLegALT31mm.stl

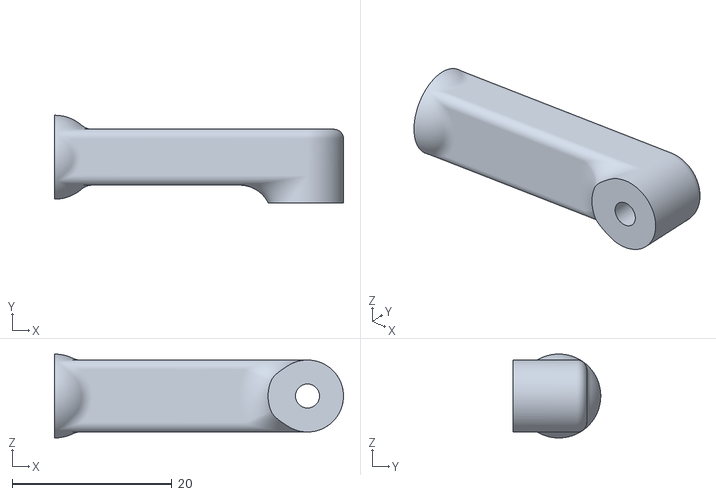
[picture p82: CAD file, 2026-05-15]
hardware/case/Alternate Case Design/Tenting Legs/files/tentingLegALT31mm.stl
36.1 x 10.9 x 10.5
