Hallaz/KLORID/hardware/case/Alternate Case Design/Tenting Legs/files/tentingLeg26mm.stl

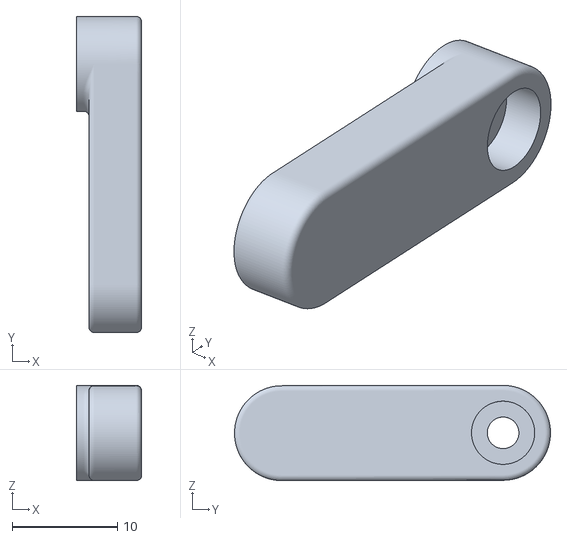
[picture p83: CAD file, 2026-05-15]
hardware/case/Alternate Case Design/Tenting Legs/files/tentingLeg26mm.stl
6.21 x 30.0 x 9.04
