Hallaz/KLORID/hardware/case/Alternate Case Design/Tenting Legs/files/tentingLegALT37mm.stl

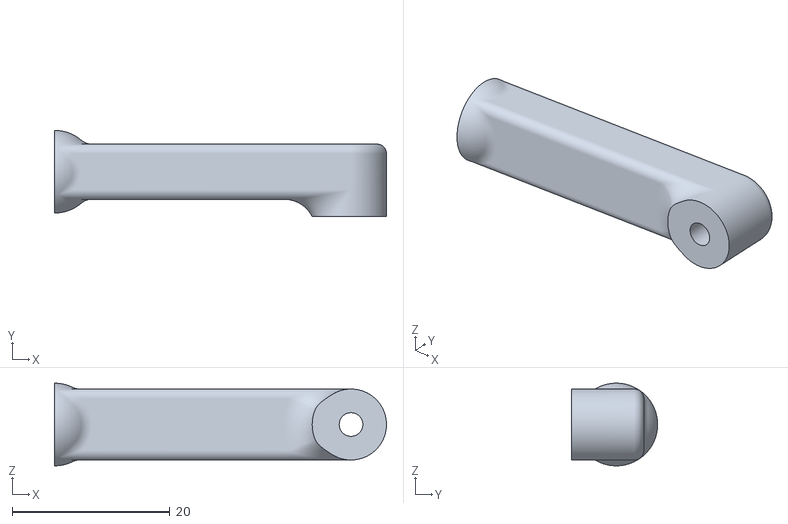
[picture p84: CAD file, 2026-05-15]
hardware/case/Alternate Case Design/Tenting Legs/files/tentingLegALT37mm.stl
42.1 x 10.9 x 10.5
