Hallaz/KLORID/hardware/docs/images/buildguide/cutouts.png

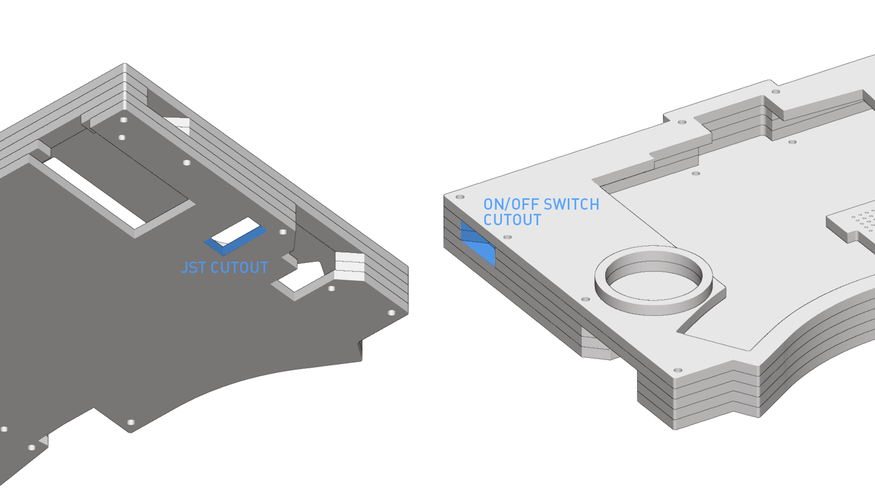
hardware/docs/images/buildguide/cutouts.png
