Hallaz/KLORID/hardware/PCB/klor1_4/klor1_4.kicad_sch

## KiCad design hardware/PCB/klor1_4/klor1_4.kicad_sch (2026-05-18)

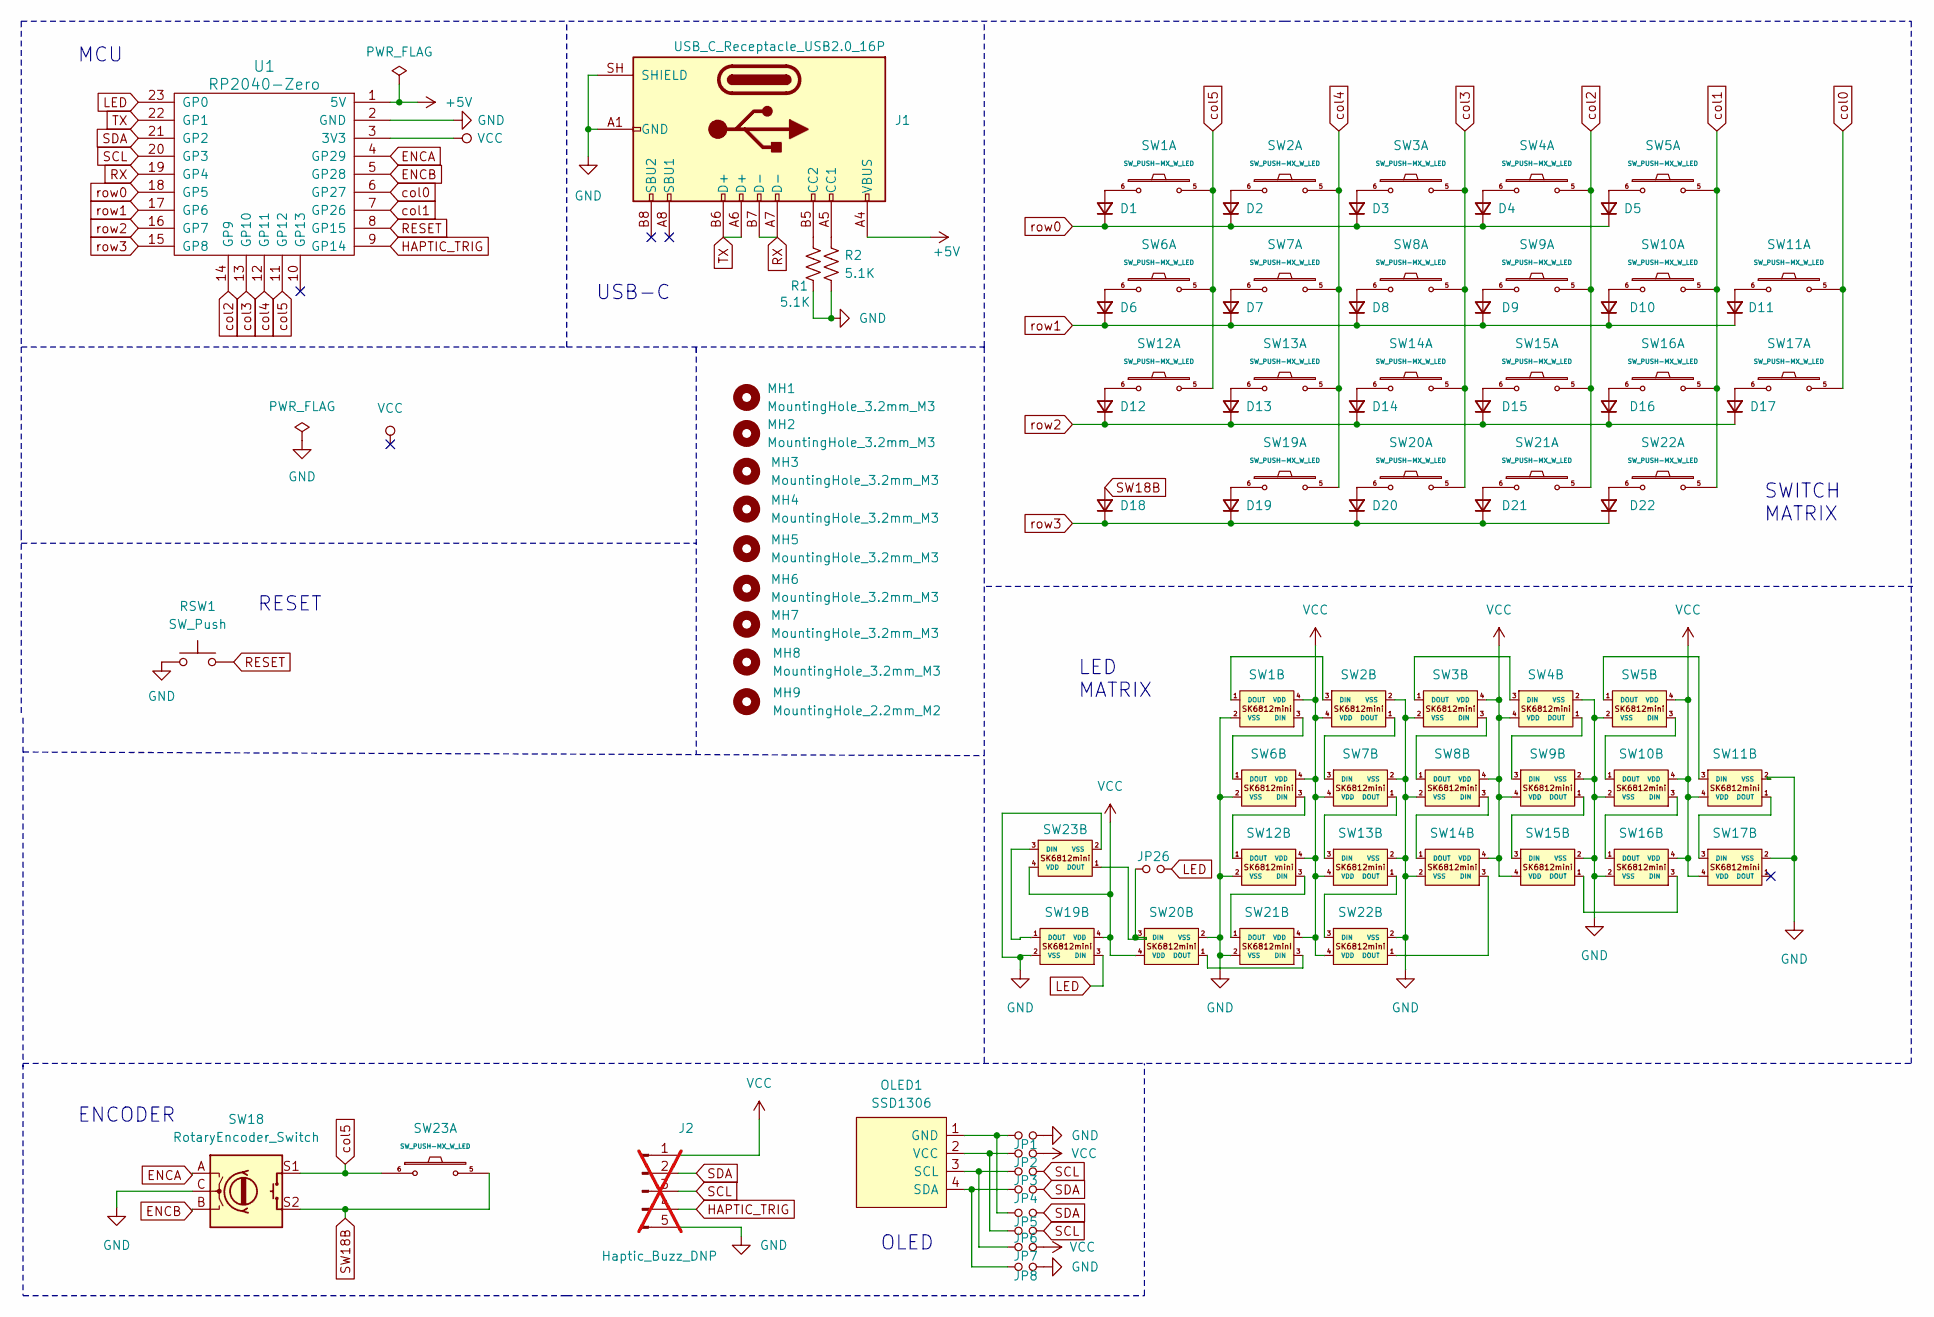
[picture p145: schematic klor1_4.kicad_sch]

Parts:
D1, D2, D3, D4, D5, D6, D7, D8, D9, D10, D11, D12, D13, D14, D15, D16, D17, D18, D19, D20, D21, D22: D_Small; Diode_SOD123
J1: USB_C_Receptacle_USB2.0_16P; USB_C_Receptacle_HRO_TYPE-C-31-M-12
J2: Haptic_Buzz_DNP; PinHeader_1x05_P2.54mm_Vertical; not fitted
JP1, JP2, JP3, JP4, JP5, JP6, JP7, JP8, JP26: Device_Jumper_NO_Small; Jumper
MH1, MH2, MH3, MH4, MH5, MH6, MH7, MH8: MountingHole_3.2mm_M3
MH9: MountingHole_2.2mm_M2
OLED1: SSD1306; SSD1306_128x64OLED
R1, R2: 5.1K; R_0603_1608Metric
RSW1: SW_Push; SW_Push_1P1T-MP_NO_Horizontal_Alps_SKRTLAE010_both_sides
SW1, SW2, SW3, SW4, SW5, SW6, SW7, SW8, SW9, SW10, SW11, SW12, SW13, SW14, SW15, SW16, SW17, SW19, SW20, SW21, SW22, SW23: SW_PUSH-MX_W_LED; SK6812MINI_and_cherry_1
SW18: RotaryEncoder_Switch; RotaryEncoder_Alps_EC11E-Switch_Vertical_H20mm-keebio_modif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
U1: RP2040-Zero

Connections:
+5V: J1.A4 (VBUS), J1.A9 (VBUS), J1.B4 (VBUS), J1.B9 (VBUS), U1.1 (5V)
ENCA: SW18.A, U1.4 (GP29)
ENCB: SW18.B, U1.5 (GP28)
GND: J1.A1 (GND), J1.A12 (GND), J1.B1 (GND), J1.B12 (GND), J1.SH (SHIELD), J2.5, JP1.2, JP8.2, R1.2, R2.2, RSW1.1, SW1.2 (VSS), SW2.2 (VSS), SW3.2 (VSS), SW4.2 (VSS), SW5.2 (VSS), SW6.2 (VSS), SW7.2 (VSS), SW8.2 (VSS), SW9.2 (VSS), SW10.2 (VSS), SW11.2 (VSS), SW12.2 (VSS), SW13.2 (VSS), SW14.2 (VSS), SW15.2 (VSS), SW16.2 (VSS), SW17.2 (VSS), SW18.C, SW19.2 (VSS), SW20.2 (VSS), SW21.2 (VSS), SW22.2 (VSS), SW23.2 (VSS), U1.2 (GND)
HAPTIC_TRIG: J2.4, U1.9 (GP14)
LED: JP26.2, SW19.3 (DIN), U1.23 (GP0)
unnamed: D1.2 (A), SW1.6
unnamed: D2.2 (A), SW2.6
unnamed: D3.2 (A), SW3.6
unnamed: D4.2 (A), SW4.6
unnamed: D5.2 (A), SW5.6
unnamed: D6.2 (A), SW6.6
unnamed: D7.2 (A), SW7.6
unnamed: D8.2 (A), SW8.6
unnamed: D9.2 (A), SW9.6
unnamed: D10.2 (A), SW10.6
unnamed: D11.2 (A), SW11.6
unnamed: D12.2 (A), SW12.6
unnamed: D13.2 (A), SW13.6
unnamed: D14.2 (A), SW14.6
unnamed: D15.2 (A), SW15.6
unnamed: D16.2 (A), SW16.6
unnamed: D17.2 (A), SW17.6
unnamed: D19.2 (A), SW19.6
unnamed: D20.2 (A), SW20.6
unnamed: D21.2 (A), SW21.6
unnamed: D22.2 (A), SW22.6
unnamed: J1.A5 (CC1), R2.1
unnamed: J1.B5 (CC2), R1.1
unnamed: JP1.1, JP5.1, OLED1.1 (GND)
unnamed: JP2.1, JP6.1, OLED1.2 (VCC)
unnamed: JP3.1, JP7.1, OLED1.3 (SCL)
unnamed: JP4.1, JP8.1, OLED1.4 (SDA)
unnamed: JP26.1, SW20.3 (DIN), SW23.1 (DOUT)
unnamed: SW1.1 (DOUT), SW2.3 (DIN)
unnamed: SW1.3 (DIN), SW6.1 (DOUT)
unnamed: SW2.1 (DOUT), SW7.3 (DIN)
unnamed: SW3.1 (DOUT), SW4.3 (DIN)
unnamed: SW3.3 (DIN), SW8.1 (DOUT)
unnamed: SW4.1 (DOUT), SW9.3 (DIN)
unnamed: SW5.3 (DIN), SW10.1 (DOUT)
unnamed: SW10.3 (DIN), SW16.1 (DOUT)
unnamed: SW11.1 (DOUT), SW17.3 (DIN)
unnamed: SW5.1 (DOUT), SW11.3 (DIN)
unnamed: SW6.3 (DIN), SW12.1 (DOUT)
unnamed: SW12.3 (DIN), SW21.1 (DOUT)
unnamed: SW13.1 (DOUT), SW22.3 (DIN)
unnamed: SW7.1 (DOUT), SW13.3 (DIN)
unnamed: SW8.3 (DIN), SW14.1 (DOUT)
unnamed: SW14.3 (DIN), SW22.1 (DOUT)
unnamed: SW15.1 (DOUT), SW16.3 (DIN)
unnamed: SW9.1 (DOUT), SW15.3 (DIN)
unnamed: SW19.1 (DOUT), SW23.3 (DIN)
unnamed: SW20.1 (DOUT), SW21.3 (DIN)
RESET: RSW1.2, U1.8 (GP15)
RX: J1.A7 (D-), J1.B7 (D-), U1.19 (GP4)
SCL: J2.3, JP3.2, JP6.2, U1.20 (GP3)
SDA: J2.2, JP4.2, JP5.2, U1.21 (GP2)
SW18B: D18.2 (A), SW18.S2, SW23.5
TX: J1.A6 (D+), J1.B6 (D+), U1.22 (GP1)
VCC: J2.1, JP2.2, JP7.2, SW1.4 (VDD), SW2.4 (VDD), SW3.4 (VDD), SW4.4 (VDD), SW5.4 (VDD), SW6.4 (VDD), SW7.4 (VDD), SW8.4 (VDD), SW9.4 (VDD), SW10.4 (VDD), SW11.4 (VDD), SW12.4 (VDD), SW13.4 (VDD), SW14.4 (VDD), SW15.4 (VDD), SW16.4 (VDD), SW17.4 (VDD), SW19.4 (VDD), SW20.4 (VDD), SW21.4 (VDD), SW22.4 (VDD), SW23.4 (VDD), U1.3 (3V3)
col0: SW11.5, SW17.5, U1.6 (GP27)
col1: SW5.5, SW10.5, SW16.5, SW22.5, U1.7 (GP26)
col2: SW4.5, SW9.5, SW15.5, SW21.5, U1.14 (GP9)
col3: SW3.5, SW8.5, SW14.5, SW20.5, U1.13 (GP10)
col4: SW2.5, SW7.5, SW13.5, SW19.5, U1.12 (GP11)
col5: SW1.5, SW6.5, SW12.5, SW18.S1, SW23.6, U1.11 (GP12)
row0: D1.1 (K), D2.1 (K), D3.1 (K), D4.1 (K), D5.1 (K), U1.18 (GP5)
row1: D6.1 (K), D7.1 (K), D8.1 (K), D9.1 (K), D10.1 (K), D11.1 (K), U1.17 (GP6)
row2: D12.1 (K), D13.1 (K), D14.1 (K), D15.1 (K), D16.1 (K), D17.1 (K), U1.16 (GP7)
row3: D18.1 (K), D19.1 (K), D20.1 (K), D21.1 (K), D22.1 (K), U1.15 (GP8)

Notes on the sheet:
SWITCH MATRIX
MCU
ENCODER
OLED
LED MATRIX
USB-C
RESET
